MrBlahhhh/esp32-autosport/sim/buck.png

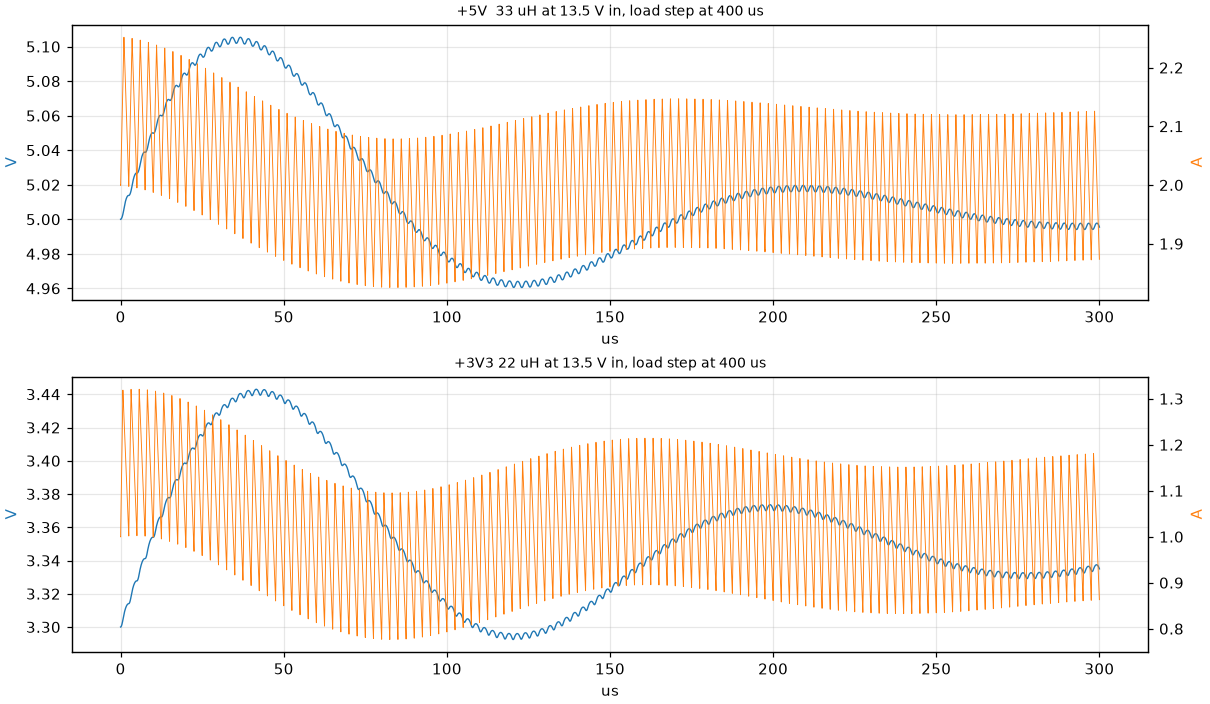
sim/buck.png
