MrBlahhhh/esp32-autosport/sim/firmware.png

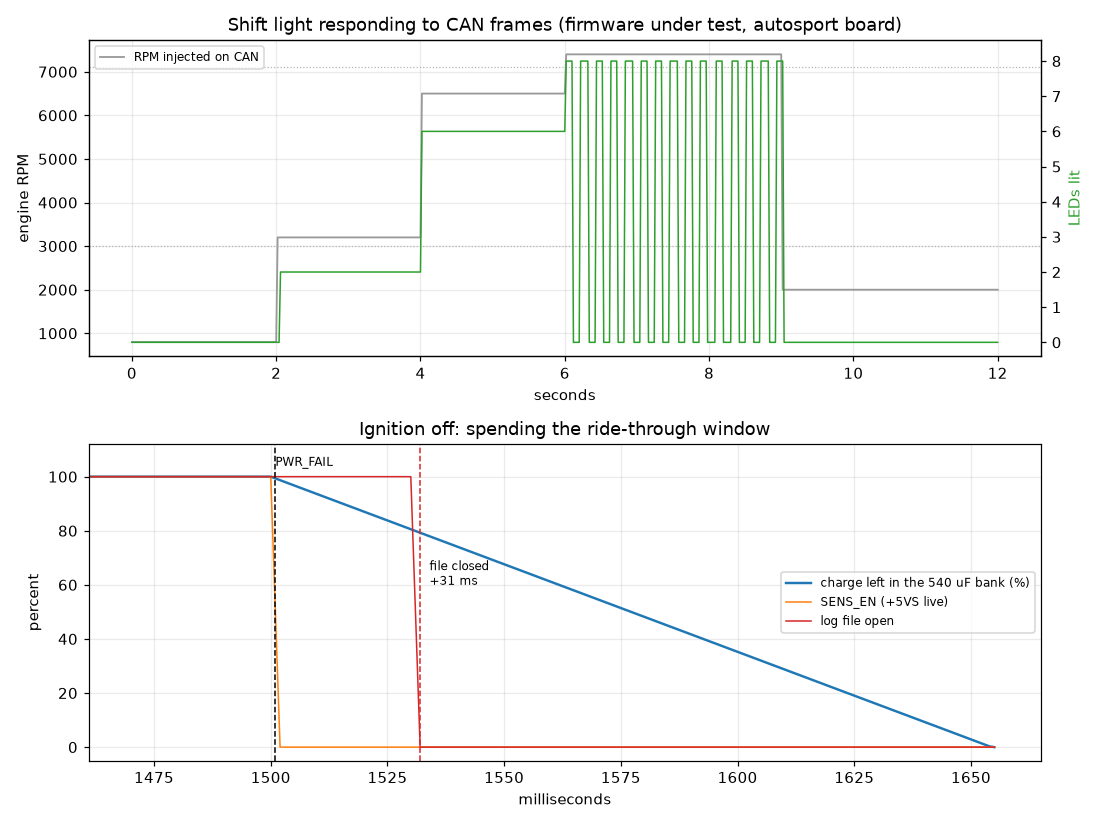
sim/firmware.png
