MrBlahhhh/esp32-autosport/sim/frontend.png

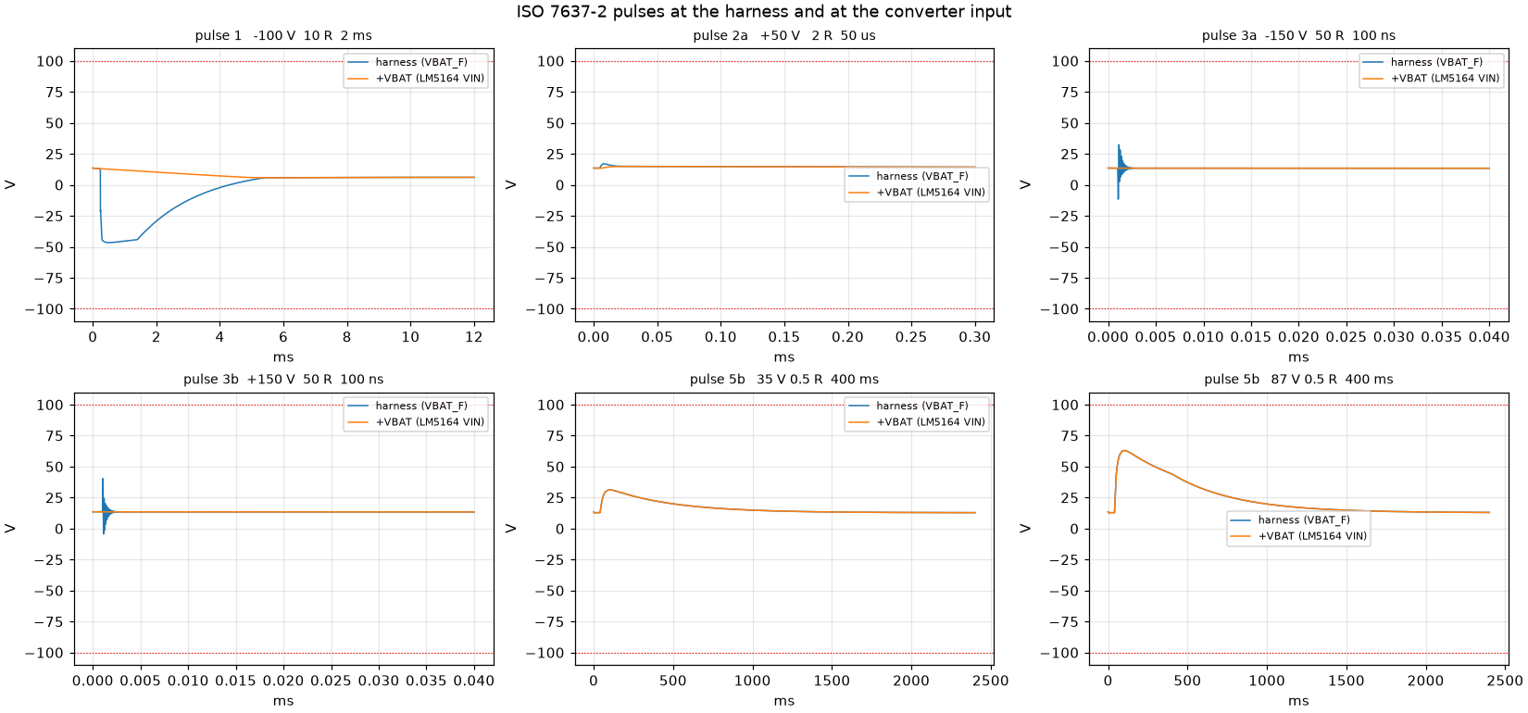
sim/frontend.png
