MrBlahhhh/esp32-autosport/gen/generate_schematic.py

#!/usr/bin/env python3
"""
Generate the KiCad schematic for the ESP32-S3 CAN + microSD automotive logger.

The netlist below is the single source of truth: every component lists its
pins and the net each pin lands on.  Symbol geometry and -- critically --
pin numbering come from the official KiCad symbol libraries, so pin numbers
are never hand-typed here.

Output: <project>/*.kicad_sch (hierarchical, one sheet per functional block),
        <project>/bom.csv, <project>/netlist.txt

Usage:  python3 gen/generate_schematic.py [--symbol-dir /usr/share/kicad/symbols]
"""

import argparse
import csv
import math
import os
import re
import uuid

# --------------------------------------------------------------------------
# S-expression reading (only what we need: pin geometry + raw symbol text)
# --------------------------------------------------------------------------

TOKEN = re.compile(r'"(?:[^"\\]|\\.)*"|\(|\)|[^\s()]+')


def parse_sexp(text):
    toks = TOKEN.findall(text)
    pos = 0

    def read():
        nonlocal pos
        tok = toks[pos]
        pos += 1
        if tok == "(":
            out = []
            while toks[pos] != ")":
                out.append(read())
            pos += 1
            return out
        return tok

    out = []
    while pos < len(toks):
        out.append(read())
    return out


def unquote(s):
    if s.startswith('"'):
        return s[1:-1].replace('\\"', '"').replace("\\\\", "\\")
    return s


def children(node, tag):
    return [c for c in node if isinstance(c, list) and c and c[0] == tag]


def _property_spans(text):
    """[(start, end)] of each top-level (property ...) block in a symbol."""
    spans = []
    depth, i, in_str = 0, 0, False
    start = None
    while i < len(text):
        ch = text[i]
        if in_str:
            if ch == "\\":
                i += 2
                continue
            if ch == '"':
                in_str = False
        elif ch == '"':
            in_str = True
        elif ch == "(":
            if depth == 1 and start is None and text.startswith("(property ", i):
                start = i
            depth += 1
        elif ch == ")":
            depth -= 1
            if depth == 1 and start is not None:
                spans.append((start, i + 1))
                start = None
        i += 1
    return spans


# The schematic format this generator emits, and the symbol-library format its
# embedded definitions were validated against.  KiCad opens older schematics and
# upgrades them on load, so emitting the 7.0 format is safe on 7, 8 and 9 alike.
SCH_FORMAT_VERSION = "20230121"          # KiCad 7.0
VALIDATED_SYMBOL_VERSION = "20241209"    # KiCad 9.0 symbol libraries


def find_symbol_dir():
    """Locate the stock KiCad symbol libraries on Windows, macOS or Linux."""
    import glob as _glob

    for var in ("KICAD9_SYMBOL_DIR", "KICAD8_SYMBOL_DIR", "KICAD7_SYMBOL_DIR",
                "KICAD6_SYMBOL_DIR"):
        path = os.environ.get(var)
        if path and os.path.isdir(path):
            return path

    patterns = [
        r"C:\Program Files\KiCad\*\share\kicad\symbols",
        r"C:\Program Files (x86)\KiCad\*\share\kicad\symbols",
        "/Applications/KiCad/KiCad.app/Contents/SharedSupport/symbols",
        "/usr/share/kicad/symbols",
        "/usr/local/share/kicad/symbols",
        os.path.expanduser("~/.local/share/kicad/*/symbols"),
    ]
    found = []
    for pat in patterns:
        found.extend(p for p in _glob.glob(pat) if os.path.isdir(p))
    if found:
        # Highest KiCad version wins when several are installed.
        return sorted(found)[-1]
    return None


class SymbolLibs:
    """Reads the installed KiCad symbol libraries."""

    def __init__(self, symbol_dir):
        self.symbol_dir = symbol_dir
        self._parsed = {}
        self._raw = {}
        self.lib_version = None

    def _load(self, lib):
        if lib in self._parsed:
            return
        path = os.path.join(self.symbol_dir, lib + ".kicad_sym")
        if not os.path.exists(path):
            raise SystemExit("symbol library not found: " + path)
        text = open(path, encoding="utf-8").read().replace("\r\n", "\n")
        root = parse_sexp(text)[0]
        ver = children(root, "version")
        if ver and self.lib_version is None:
            self.lib_version = unquote(ver[0][1])
        self._parsed[lib] = {unquote(s[1]): s for s in children(root, "symbol")}

        # Byte-exact source text for each top-level symbol, so the definitions
        # we embed in the schematic are identical to the library's.
        # One indent level is two spaces (7.0 libraries) or one tab (9.0).
        raw = {}
        for m in re.finditer(r'^(?:  |\t)\(symbol "([^"]+)"', text, re.M):
            start = m.start()
            depth, i, in_str = 0, start, False
            while i < len(text):
                ch = text[i]
                if in_str:
                    if ch == "\\":
                        i += 2
                        continue
                    if ch == '"':
                        in_str = False
                elif ch == '"':
                    in_str = True
                elif ch == "(":
                    depth += 1
                elif ch == ")":
                    depth -= 1
                    if depth == 0:
                        i += 1
                        break
                i += 1
            raw[m.group(1)] = text[start:i]
        self._raw[lib] = raw

    def symbol(self, lib_id):
        lib, name = lib_id.split(":", 1)
        self._load(lib)
        if name not in self._parsed[lib]:
            raise SystemExit("symbol not found: " + lib_id)
        return self._parsed[lib][name]

    def has(self, lib_id):
        lib, name = lib_id.split(":", 1)
        if not os.path.exists(os.path.join(self.symbol_dir, lib + ".kicad_sym")):
            return False
        self._load(lib)
        return name in self._parsed[lib]

    def extends(self, lib_id):
        ext = children(self.symbol(lib_id), "extends")
        return unquote(ext[0][1]) if ext else None

    def properties(self, lib_id):
        out = {}
        for prop in children(self.symbol(lib_id), "property"):
            out[unquote(prop[1])] = unquote(prop[2])
        return out

    def raw(self, lib_id):
        """Library source for the symbol, renamed to its full lib_id.

        A schematic's lib_symbols cache cannot express `extends`: KiCad stores
        derived symbols flattened.  KiCad's own flattening keeps the parent's
        geometry but the child's property fields verbatim (positions and text
        effects included), so the splice must swap whole property blocks or
        ERC flags the cached copy as differing from the library's.
        """
        lib, name = lib_id.split(":", 1)
        self._load(lib)
        parent = self.extends(lib_id)
        if parent is None:
            text = self._raw[lib][name]
            return text.replace('(symbol "%s"' % name,
                                '(symbol "%s:%s"' % (lib, name), 1)

        text = self._raw[lib][parent]
        child = self._raw[lib][name]
        pspans = _property_spans(text)
        child_props = [child[a:b] for a, b in _property_spans(child)]
        if pspans and child_props:
            first, last = pspans[0][0], pspans[-1][1]
            indent = text[:first].rsplit("\n", 1)[-1]
            text = text[:first] + ("\n" + indent).join(child_props) + text[last:]
        # Sub-symbol names must follow the derived symbol, e.g. FOO_1_1.
        text = text.replace('(symbol "%s_' % parent, '(symbol "%s_' % name)
        text = text.replace('(symbol "%s"' % parent,
                            '(symbol "%s:%s"' % (lib, name), 1)
        return text

    def pins(self, lib_id):
        """[(number, name, local_x, local_y, angle, hidden)] resolving `extends`.

        Hidden pins matter: the ESP32 module symbol carries its GND pin 40 and
        exposed pad 41 as hidden pins that KiCad ties to GND by name.  We record
        them so the netlist documents the connection, but never draw a stub to
        an invisible pin.
        """
        parent = self.extends(lib_id)
        if parent:
            lib = lib_id.split(":", 1)[0]
            return self.pins(lib + ":" + parent)
        out = []
        for unit in children(self.symbol(lib_id), "symbol"):
            for pin in children(unit, "pin"):
                at = children(pin, "at")[0]
                num = unquote(children(pin, "number")[0][1])
                nam = unquote(children(pin, "name")[0][1])
                out.append((num, nam, float(at[1]), float(at[2]),
                            int(float(at[3])), "hide" in pin))
        return out


# --------------------------------------------------------------------------
# Geometry helpers
# --------------------------------------------------------------------------

def rotate(theta, vx, vy):
    """Rotate a sheet-space vector by the symbol placement angle (CCW, Y down)."""
    theta %= 360
    if theta == 0:
        return (vx, vy)
    if theta == 90:
        return (vy, -vx)
    if theta == 180:
        return (-vx, -vy)
    if theta == 270:
        return (-vy, vx)
    raise ValueError("unsupported rotation %r" % theta)


def pin_geometry(local_x, local_y, angle, theta):
    """Return (offset_from_origin, outward_unit_vector) in sheet space."""
    # Symbol space has Y up; the sheet has Y down.
    off = rotate(theta, local_x, -local_y)
    # A pin's `angle` points from its connection end *into* the body, so the
    # free (wire) direction is the opposite.
    out_ang = math.radians(angle + 180)
    d = rotate(theta, round(math.cos(out_ang)), -round(math.sin(out_ang)))
    return off, d


# Rails get a power symbol rather than a net-name label. It is what every
# schematic does, it makes a rail readable at a glance, and it removes the
# single largest source of labels on the page -- GND alone accounted for
# hundreds. Where KiCad has no stock symbol for a rail (+VBAT, +5VS, SD_VDD)
# a generic one is instantiated and its Value overridden: for a power symbol
# KiCad takes the net name from the Value field, so the rail is named
# correctly and drawn correctly. gen/validate.py re-extracts the netlist
# through KiCad and compares it node-for-node, so if that were wrong the
# build would fail rather than quietly merge two rails.
RAILS = {
    "GND":    ("power:GND",   "GND"),
    "+3V3":   ("power:+3V3",  "+3V3"),
    "+5V":    ("power:+5V",   "+5V"),
    "VBUS":   ("power:VBUS",  "VBUS"),
    "+VBAT":  ("power:+BATT", "+VBAT"),
    "+5VS":   ("power:+BATT", "+5VS"),
    "SD_VDD": ("power:+BATT", "SD_VDD"),
}


def power_placement(libs, lib_id, ex, ey, d):
    """Where to put a power symbol so its pin lands at (ex, ey) facing -d."""
    angle = libs.pins(lib_id)[0][4]
    want = (-d[0], -d[1])
    for theta in (0, 90, 180, 270):
        off, ds = pin_geometry(0.0, 0.0, angle, theta)
        if ds == want:
            return snap(ex - off[0]), snap(ey - off[1]), theta
    return snap(ex), snap(ey), 0


# --------------------------------------------------------------- wiring ----
# A net drawn as two name labels is correct and unreadable. Where a net has
# exactly two pins in the whole design and both are on one sheet, the two
# parts can simply be placed next to each other and joined with a wire --
# which is what the connection actually is. Everything else (rails, shared
# nodes, anything crossing a sheet) keeps a symbol or a label, because those
# genuinely are one-to-many.

def pin_count(net):
    n = 0
    for sh in SHEETS:
        for p in sh["parts"]:
            n += sum(1 for v in p["pins"].values() if v == net)
    return n


def wire_pairs(sh):
    """[(partA, pinA, partB, pinB, net)] for this sheet's two-pin nets."""
    here = [p for p in sh["parts"] if not p["prefix"].startswith("#")]
    out, used = [], set()
    for net in sorted({v for p in here for v in p["pins"].values()}):
        if net in RAILS or pin_count(net) != 2:
            continue
        ends = [(p, num) for p in here for num, v in p["pins"].items() if v == net]
        if len(ends) != 2:
            continue                      # the other end is on another sheet
        (pa, na), (pb, nb) = ends
        if pa["ref"] in used or pb["ref"] in used:
            continue                      # one cluster per part keeps it simple
        used.add(pa["ref"])
        used.add(pb["ref"])
        out.append((pa, na, pb, nb, net))
    return out


def label_rotation(direction):
    return {(1, 0): 0, (-1, 0): 180, (0, -1): 90, (0, 1): 270}[direction]


def label_justify(direction):
    """Which way the text runs from the anchor.

    Every label used to be justified left, so one pointing back at its own
    component ran its text straight over the body -- RON_5V across R4,
    SW_5V across L1. Text has to run away from the part, not into it.
    """
    return "right" if direction in ((-1, 0), (0, 1)) else "left"


def mm(v):
    v = round(v, 4)
    return ("%f" % v).rstrip("0").rstrip(".") or "0"


NS = uuid.UUID("6f1d7d1e-6d3e-5a2b-9c44-2b6f0f0a1c77")


def det_uuid(key):
    return str(uuid.uuid5(NS, key))


# --------------------------------------------------------------------------
# Board description
# --------------------------------------------------------------------------

PROJECT = "esp32s3-can-sd-logger"
TITLE = "ESP32-S3 CAN + microSD Automotive Logger"
REV = "B"
DATE = "2026-08-11"   # the date of the last electrical change, not of the
                      # last regeneration -- update it when the netlist moves
COMPANY = "geekopolis"

R0805 = "Resistor_SMD:R_0805_2012Metric"
C0805 = "Capacitor_SMD:C_0805_2012Metric"
C1206 = "Capacitor_SMD:C_1206_3216Metric"
SOT23 = "Package_TO_SOT_SMD:SOT-23"
SOT236 = "Package_TO_SOT_SMD:SOT-23-6"
# NOTE: confirm the exposed-pad size against TI's DDA package drawing before layout.
# TI DDA0008B (SO PowerPAD-8): pad max 2.71x3.4mm, TI land 2.95x4.9mm copper
# with a 2.71x3.4mm solder-mask-defined opening -- this footprint matches it.
SO8EP = ("Package_SO:SOIC-8-1EP_3.9x4.9mm_P1.27mm_"
         "EP2.95x4.9mm_Mask2.71x3.4mm_ThermalVias")
SOIC8 = "Package_SO:SOIC-8_3.9x4.9mm_P1.27mm"
SMC = "Diode_SMD:D_SMC"
SMA = "Diode_SMD:D_SMA"
SOD123 = "Diode_SMD:D_SOD-123"
LED0805 = "LED_SMD:LED_0805_2012Metric"
JST4 = "Connector_JST:JST_PH_B4B-PH-K_1x04_P2.00mm_Vertical"
JST8 = "Connector_JST:JST_PH_B8B-PH-K_1x08_P2.00mm_Vertical"
HDR3 = "Connector_PinHeader_2.54mm:PinHeader_1x03_P2.54mm_Vertical"
HDR4 = "Connector_PinHeader_2.54mm:PinHeader_1x04_P2.54mm_Vertical"
HDR6 = "Connector_PinHeader_2.54mm:PinHeader_1x06_P2.54mm_Vertical"
HDR8 = "Connector_PinHeader_2.54mm:PinHeader_1x08_P2.54mm_Vertical"
SOT235 = "Package_TO_SOT_SMD:SOT-23-5"
SOT233 = "Package_TO_SOT_SMD:SOT-23"   # TLV431 is a 3-pin SOT-23
SJ2 = "Jumper:SolderJumper-2_P1.3mm_Open_Pad1.0x1.5mm"
SJ2B = "Jumper:SolderJumper-2_P1.3mm_Bridged_Pad1.0x1.5mm"
SJ3 = "Jumper:SolderJumper-3_P1.3mm_Open_Pad1.0x1.5mm"
SJ3B12 = "Jumper:SolderJumper-3_P1.3mm_Bridged12_Pad1.0x1.5mm"
TP = "TestPoint:TestPoint_Pad_D1.5mm"
MH = "MountingHole:MountingHole_3.2mm_M3"

# Each entry: (lib_id, value, footprint, {pin: net}, mpn, note)
SHEETS = []


def sheet(name, filename, description):
    s = {"name": name, "file": filename, "desc": description, "parts": []}
    SHEETS.append(s)
    return s


_TOL_RE = re.compile(r"\s+(\d+(?:\.\d+)?\s*%)$")
_VOLT_RE = re.compile(r"\s+(\d+(?:\.\d+)?\s*V)$")


def split_value(value):
    """'100nF 16V' -> ('100nF', '16V', ''), '1k 0.1%' -> ('1k', '', '0.1%').

    A rating packed into the VALUE field is invisible to anything that
    parses the schematic: a review tool reading "1k 0.1%" sees no usable
    resistance and reports the part as unvalued, which is what happened to
    34 capacitors and 16 resistors here. Only a trailing voltage or
    tolerance token is peeled off, so "600R" and
    "0.2A PTC" are left exactly as they are.
    """
    tol = volt = ""
    m = _TOL_RE.search(value)
    if m:
        tol = m.group(1).replace(" ", "")
        value = value[:m.start()]
    m = _VOLT_RE.search(value)
    if m:
        volt = m.group(1).replace(" ", "")
        value = value[:m.start()]
    return value.strip(), volt, tol


# Part numbers for the generic passives and the two ferrites.
#
# These used to be left blank on the theory that JLC's order flow auto-matches
# an 0805 resistor from value + package, which it does. That stopped being good
# enough the moment the boards were going to be hand-assembled: buying the
# parts loose needs a real number for every line, not just the interesting
# ones. Every entry below is the part JLCPCB's own matcher chose on a live
# order run (2026-08-13), so ordering from LCSC gets the same component the
# assembly house would have fitted.
#
# Keyed on the Comment string export_fab.py writes, which is value + voltage +
# tolerance -- so 100nF100V and 100nF16V stay distinct. That distinction is
# load-bearing: C2/C5/C16 sit on +VBAT and must be the 100 V part.
GENERIC_LCSC = {
    "0466002.NR": "C187595",
    "100": "C17408",
    "100k": "C149504",
    "100k1%": "C5713386",
    "100nF100V": "C28233",
    "100nF16V": "C49678",
    "10k": "C17414",
    "10k0.1%": "C856630",
    "10nF100V": "C128805",
    "10uF100V": "C6872041",
    "10uF16V": "C13585",
    "12.7k1%": "C2933300",
    "121k": "C17438",
    "15k0.1%": "C728642",
    "1M": "C17514",
    "1k": "C17513",
    "1k0.1%": "C864177",
    "1nF50V": "C46653",
    "1uF16V": "C28323",
    "1uF50V": "C28323",
    "2.21k0.1%": "C865368",
    "2.2nF50V": "C28260",
    "2.49k": "C2930178",
    "20.5k": "C2933365",
    "22uF16V": "C12891",
    "27.4k1%": "C2930188",
    "270pF50V": "C1732",
    "31.6k": "C49254250",
    "33": "C17634",
    "4.7k": "C17673",
    "4.7nF50V": "C1744",
    "44.2k": "C2960780",
    "47k": "C17713",
    "5.1k": "C27834",
    "57.6k": "C163405",
    "60.4": "C72998",
    "742792022": "C2661452",
    "742792625": "C1533835",
    "8.2k": "C17828",
    "95.3k": "C2930435",
}


def part(sh, prefix, lib_id, value, footprint, pins, mpn="", note="", nc=(),
         lcsc=""):
    base, volt, tol = split_value(value)
    sh["parts"].append(
        {
            "prefix": prefix,
            "lib_id": lib_id,
            "value": base,
            "voltage": volt,
            "tolerance": tol,
            "footprint": footprint,
            "pins": pins,
            "mpn": mpn,
            "note": note,
            "nc": set(nc),
            # Fall back to the generic table, keyed the same way export_fab.py
            # builds its Comment column (value + voltage + tolerance).
            # ...or by bare MPN. export_fab.py drops the manufacturer from
            # the Comment ("Wurth 742792022" -> "742792022"), so match the
            # last token too.
            "lcsc": lcsc or GENERIC_LCSC.get(base + volt + tol)
                    or GENERIC_LCSC.get(mpn)
                    or GENERIC_LCSC.get(mpn.split()[-1] if mpn else "", ""),
        }
    )


def R(sh, value, a, b, mpn="", note="", fp=R0805):
    part(sh, "R", "Device:R", value, fp, {"1": a, "2": b}, mpn, note)


def C(sh, value, a, b, fp=C0805, mpn="", note="", polarized=False):
    """`a` is pin 1. For a polarized part that is the + terminal, and the
    symbol must say so: a plain Device:C on an electrolytic land is right
    by luck rather than by construction, and neither ERC nor a reader can
    tell it from a reversed one."""
    lib = "Device:C_Polarized" if polarized else "Device:C"
    part(sh, "C", lib, value, fp, {"1": a, "2": b}, mpn, note)


def flag(sh, net):
    part(sh, "#FLG", "power:PWR_FLAG", "PWR_FLAG", "", {"1": net}, note="ERC power-source flag")


# ---------------------------------------------------------------- power ----
pw = sheet(
    "Power",
    "power.kicad_sch",
    "Reverse-battery protection, transient clamping, +5V / +3V3 / +5V sensor rails",
)

part(pw, "J", "Connector_Generic:Conn_01x04", "PWR + CAN harness", JST4,
     {"1": "VBAT_IN", "2": "GND", "3": "CAN_H", "4": "CAN_L"},
     "JST B4B-PH-K-S(LF)(SN)", "Pin 1 +12V, 2 GND, 3 CAN_H, 4 CAN_L "
     "(Autosport Labs harness order)", lcsc="C131334")
part(pw, "F", "Device:Fuse", "2A slow", "Fuse:Fuse_1206_3216Metric",
     {"1": "VBAT_IN", "2": "VBAT_F"}, "Littelfuse 0466002.NR",
     "Sacrificial: only opens on a hard fault, not on reverse polarity")
part(pw, "FB", "Device:L", "600R", "Inductor_SMD:L_1206_3216Metric",
     {"1": "VBAT_F", "2": "VBAT_FB"}, "Wurth 742792625", "Conducted-emissions bead")

# Ideal-diode reverse-battery block
part(pw, "U", "Power_Management:LM74700", "LM74700-Q1", SOT236,
     {"1": "VCAP", "2": "GND", "3": "VBAT_UVLO", "4": "+VBAT", "5": "GATE_RB", "6": "VBAT_FB"},
     "LM74700QDBVRQ1", "Ideal-diode controller; blocks reverse battery via Q1",
     lcsc="C2941042")
part(pw, "Q", "Device:Q_NMOS_GSD", "IPD068N10", "Package_TO_SOT_SMD:TO-252-3_TabPin2",
     {"1": "GATE_RB", "2": "VBAT_FB", "3": "+VBAT"}, "Infineon IPD068N10N3G",
     "Source to battery, drain to load: body diode blocks reverse polarity. "
     "The previously specified PSMN4R3-100BSE does not exist", lcsc="C88066")
C(pw, "1uF 50V", "VCAP", "VBAT_FB", mpn="", note="LM74700 charge-pump reservoir")
C(pw, "100nF 100V", "VBAT_FB", "GND",
  note="LM74700 ANODE input capacitor: the datasheet requires a minimum "
       "22nF at ANODE and this node is behind FB1 with nothing else on it")
R(pw, "100k", "VBAT_FB", "VBAT_UVLO", note="UVLO upper leg")
R(pw, "44.2k", "VBAT_UVLO", "GND",
  note="UVLO lower leg. Ratio 0.3065 against V_EN_IH 1.06/2.0/2.6V gives "
       "release at 3.5/6.5/8.5V. The earlier 25.5k assumed a 1.2V threshold "
       "and would not have started until 9.8V typical, 12.8V worst case")

# Ahead of Q1, not behind it. Clamping downstream of the reverse-battery FET
# leaves Q1 and the LM74700 exposed to whatever arrives on the harness: on a
# negative transient Q1 turns off and stands the whole pulse across its
# drain-source, and ISO 7637-2 pulse 1 (-100V) and 3a (-150V) both exceed its
# 100V rating. In front of the FET the clamp catches those first.
#
# Bidirectional, because a unidirectional part here would forward-conduct on
# a sustained reverse connection and blow the fuse -- which is exactly the
# outcome the ideal diode exists to avoid. SMCJ40CA stands off 40V either
# way, so -14V reverse battery is still Q1's job to block, and only real
# transients are clamped.
part(pw, "D", "Device:D_TVS", "SMCJ40CA", SMC, {"1": "VBAT_F", "2": "GND"},
     "Littelfuse SMCJ40CA",
     "40V standoff / 64.5V clamp @ 1500W, bidirectional: absorbs ISO 7637-2 "
     "pulse 5b load dump and the negative pulses, ahead of the FET. 40V not "
     "33V so the part stands off the declared 36V input top", lcsc="C80273")
C(pw, "100uF 100V", "+VBAT", "GND", fp="Capacitor_SMD:CP_Elec_10x10.5",
  mpn="Nichicon UCD2A101MNL1GS", polarized=True,
  note="Bulk hold-up; any 100uF >=80V SMD electrolytic on a 10x10.5 land "
       "works -- match in the JLC catalog at order. Pin 1 is +")
C(pw, "10uF 100V", "+VBAT", "GND", fp=C1206, note="Switcher input bypass")
C(pw, "100nF 100V", "+VBAT", "GND", note="HF bypass")

# Ride-through bank. The card in this thing is written continuously and the
# ignition is switched, so every drive ends in an unannounced power cut. With
# only the 100uF above, +VBAT falls through the converters' UVLO about 12 ms
# after the harness opens -- less than one SD block write on a slow card, so
# the file is left however the card happened to leave it.
#
# Energy is 0.5*C*(V^2 - Vmin^2), so it belongs here on +VBAT rather than on
# a 3.3V rail: the same capacitance is worth fifteen times as much at 12 V as
# it is at 3.3 V. From 12 V (the low end of a healthy battery) down to the
# 7 V the converters stop regulating at, 760 uF holds 36.1 mJ.
#
# 760 uF (100 + 2 x 330), not 540: the 16x22 can has the same land pattern as
# the 16x17.5 it replaces, so the extra 220 uF is free in copper. It is not
# free in inrush -- charging the bank through Q1's body diode gives the fuse
# an I2t burden proportional to C, so the 2 A nano fuse's margin drops from
# about 5x to about 3.6x. Still comfortable, but it is the number to watch if
# the bank ever grows again (gen/simulate.py, inrush study).
#
# 100 V rated, not 63 V: D1 clamps at 64.5 V and the declared input window
# already goes to 36 V.
for _ in range(2):
    C(pw, "330uF 100V", "+VBAT", "GND",
      fp="Capacitor_SMD:CP_Elec_16x22", polarized=True,
      note="Power-fail ride-through. With the sensor rail shed and the LEDs "
           "off the board draws about 0.35 W here, so the bank holds the "
           "rails up long enough to finish the block in flight and close the "
           "file. 16x22 rather than 16x17.5: the two footprints are identical "
           "in every copper and courtyard layer -- only the can is 4.5 mm "
           "taller -- so the extra 220 uF costs nothing but enclosure height. "
           "Any 330uF >=80V on a 16 mm land works; match in the JLC catalogue "
           "at order. Pin 1 is +")

# ---- power-fail detect ---------------------------------------------------
# Sensed on VBAT_F, ahead of Q1, which is the whole point: when the ignition
# opens, the harness side collapses at once while +VBAT coasts on the bank
# above. Q1 is already the isolating diode between them, so this costs no
# extra parts and gives the earliest possible warning. Sensing +VBAT instead
# would only notice once the ride-through had already started being spent.
#
# A bare divider into a GPIO will not do. The ESP32's input is only
# guaranteed high above 0.75*VDD and low below 0.25*VDD, so the real trip
# point could land anywhere from 11 V down to 3.7 V of harness -- and at
# 3.7 V the bank is long empty. The shunt reference makes it +/-1%.
R(pw, "100k 1%", "VBAT_F", "PFD_SENSE", note="Power-fail divider, upper leg")
R(pw, "12.7k 1%", "PFD_SENSE", "GND",
  note="Lower leg: trips at 1.24V * 112.7/12.7 = 11.00V on the harness, "
       "below anything a healthy battery does and far above the converters' "
       "dropout, so there is a whole ride-through between detect and death")
part(pw, "U", "Reference_Voltage:TL431DBZ", "TLV431A", SOT233,
     {"1": "PWR_FAIL", "2": "PFD_SENSE", "3": "GND"},
     "TLV431ASN1T1G",
     "Power-fail comparator. Below the trip point it stops conducting and "
     "R_pu takes PWR_FAIL high, so the interrupt is a rising edge and an "
     "absent or dead part reads as 'failing' rather than as 'fine'. "
     "PINOUT: this uses KiCad's TL431DBZ numbering (1 K, 2 REF, 3 A) on a "
     "plain SOT-23. Shunt references are NOT consistent between vendors in "
     "this package -- CONFIRM against the datasheet for the exact part "
     "ordered. If REF and A are swapped the part simply never conducts and "
     "PWR_FAIL sits permanently asserted: loud, harmless, and obvious on the "
     "bench, but it will not be caught by ERC or DRC", lcsc="C127592")
R(pw, "10k", "+3V3", "PWR_FAIL",
  note="Cathode pull-up. 10k gives the part 330uA, over the TLV431's 100uA "
       "minimum cathode current. A 2.5V TL431 would need 1mA and so a 2.2k "
       "here, and the divider below would have to change with it")
R(pw, "1M", "PWR_FAIL", "PFD_SENSE",
  note="Hysteresis, about 0.3V at the harness. Without it a battery sagging "
       "across the threshold on crank would chatter the interrupt")
C(pw, "1nF 50V", "PFD_SENSE", "GND",
  note="Just enough to keep switching noise off the reference. Larger would "
       "delay the very detection this exists to make early")

# ---- switched sensor excitation -----------------------------------------
# The ride-through only works if the load goes away with the power. LEDs and
# the SD card are firmware's to shed, but sensors on +5VS are external and
# draw whatever they draw -- four at 20 mA is 400 mW, which more than doubles
# the drain and would halve the numbers above. This switch is what makes the
# shed possible.
#
# Off by default: the gate is pulled to +5V through R_g, so the rail comes up
# only when firmware asserts SENS_EN, and it drops the instant the MCU stops
# driving. That is the correct failure direction for a rail that feeds a loom.
part(pw, "Q", "Device:Q_PMOS_GSD", "AO3401A", SOT23,
     {"1": "SENS_G", "2": "+5V", "3": "VSENS_SW"}, "Alpha & Omega AO3401A",
     "Sensor-rail load switch. Source to +5V, so the body diode points into "
     "the rail and the switch blocks with the gate high", lcsc="C15127")
R(pw, "100k", "+5V", "SENS_G", note="Holds the switch off when nothing drives it")
part(pw, "Q", "Device:Q_NMOS_GSD", "2N7002", SOT23,
     {"1": "SENS_EN_G", "2": "GND", "3": "SENS_G"}, "onsemi 2N7002",
     "Level shifter: the P-FET's gate has to be pulled to GND from 5V, and "
     "a 3.3V GPIO cannot do that directly", lcsc="C8545")
R(pw, "10k", "SENS_EN", "SENS_EN_G", note="GPIO series/gate resistor")
R(pw, "100k", "SENS_EN_G", "GND",
  note="Holds the level shifter off while the MCU is in reset")

# +5V rail
part(pw, "U", "Regulator_Switching:LM5164DDA", "LM5164 (5V)", SO8EP,
     {"1": "GND", "2": "+VBAT", "3": "EN_5V", "4": "RON_5V", "5": "FB_5V",
      "6": "PG_5V", "7": "BST_5V", "8": "SW_5V", "9": "GND"},
     "LM5164DDAR", "100V synchronous buck, ultra-low Iq. Non-automotive "
     "variant; the Q1 is scarce", lcsc="C477928")
R(pw, "100k", "+VBAT", "EN_5V", note="Enable tied to VIN (LM74700 already gates on UVLO)")
C(pw, "10nF 100V", "EN_5V", "GND", note="EN sits on a bare 100k to VBAT; this "
  "keeps a high-impedance enable node quiet in a vehicle")
R(pw, "31.6k", "RON_5V", "GND",
  note="RON = 5.0V x 2500 / 400kHz (Eq 12) -> 396kHz; tON = 237ns at the "
       "53.3V clamp, comfortably above the 50ns minimum")
C(pw, "2.2nF 50V", "BST_5V", "SW_5V",
  note="Bootstrap: datasheet mandates exactly 2.2nF X7R -- a larger value "
       "overstresses the internal VCC regulator and damages the device")
part(pw, "L", "Device:L", "33uH", "Inductor_SMD:L_Sunlord_SWPA8040S",
     {"1": "SW_5V", "2": "+5V"}, "Sunlord ASWPA8050S330MT",
     "Shielded molded, Isat 3A vs the 1.75A max peak limit", lcsc="C340244")
R(pw, "100k", "+5V", "FB_5V", note="FB upper: 1.2V ref -> 5.00V")
R(pw, "31.6k", "FB_5V", "GND", note="FB lower")
# Type-3 ripple injection (datasheet Table 6-1): the all-ceramic output has no
# ESR ripple for the COT comparator, so a SW-node RC ramp is AC-coupled into
# FB. Sized for ~20mV at FB with VIN = 14V nominal, per TI's design example.
R(pw, "121k", "SW_5V", "RAMP_5V", note="Ripple-injection ramp resistor RA")
C(pw, "2.2nF 50V", "RAMP_5V", "+5V", note="Ramp capacitor CA. 2.2nF, not 3.3nF: at 8 V in the injected ramp was 10.6 mV against the ~15 mV COT floor; the smaller CA buys x1.5")
C(pw, "270pF 50V", "RAMP_5V", "FB_5V", note="Ramp coupling capacitor CB")
C(pw, "22uF 16V", "+5V", "GND", fp=C1206)
C(pw, "22uF 16V", "+5V", "GND", fp=C1206)
C(pw, "100nF 16V", "+5V", "GND")
R(pw, "100k", "PG_5V", "+3V3", note="Power-good pull-up")

# +3V3 rail
part(pw, "U", "Regulator_Switching:LM5164DDA", "LM5164 (3V3)", SO8EP,
     {"1": "GND", "2": "+VBAT", "3": "EN_3V3", "4": "RON_3V3", "5": "FB_3V3",
      "6": "PG_3V3", "7": "BST_3V3", "8": "SW_3V3", "9": "GND"},
     "LM5164DDAR", "Second buck straight off the battery: a shorted 5V "
     "sensor harness cannot brown out the MCU", lcsc="C477928")
# This converter's own input capacitors. It had none: it shared the 5 V
# island's pair, 12.6 mm away across the board, which puts that whole
# distance in the switching loop. The LM5164 chops the full battery
# voltage in nanoseconds, and the loop inductance turns into VIN ringing
# and radiated noise. Two more parts is a cheap fix for it.
C(pw, "100nF 100V", "+VBAT", "GND",
  note="3V3 buck HF input bypass -- must sit at U3's VIN pin")
C(pw, "10uF 100V", "+VBAT", "GND", fp=C1206,
  note="3V3 buck bulk input, at the VIN pin")
R(pw, "100k", "+VBAT", "EN_3V3")
C(pw, "10nF 100V", "EN_3V3", "GND", note="EN noise immunity, as for the 5V rail")
R(pw, "20.5k", "RON_3V3", "GND",
  note="RON = 3.3V x 2500 / 400kHz (Eq 12) -> 402kHz; tON = 154ns at the "
       "53.3V clamp, above the 50ns minimum")
C(pw, "2.2nF 50V", "BST_3V3", "SW_3V3",
  note="Bootstrap: datasheet-mandated 2.2nF X7R, do not increase")
part(pw, "L", "Device:L", "22uH", "Inductor_SMD:L_Sunlord_SWPA8040S",
     {"1": "SW_3V3", "2": "+3V3"}, "Sunlord ASWPA8050S220MT",
     "Same automotive series as L1. C340243 verified against the live JLC "
     "catalogue 2026-08-12: 22uH, 3A Isat, 8x8mm -- one part number below "
     "L1's C340244, which is the 33uH of the same series",
     lcsc="C340243")
R(pw, "100k", "+3V3", "FB_3V3", note="FB upper: 1.2V ref -> 3.28V")
R(pw, "57.6k", "FB_3V3", "GND", note="FB lower")
R(pw, "95.3k", "SW_3V3", "RAMP_3V3", note="Ripple-injection ramp resistor RA")
C(pw, "2.2nF 50V", "RAMP_3V3", "+3V3", note="Ramp capacitor CA, sized as on the 5 V rail for ramp amplitude at low battery")
C(pw, "270pF 50V", "RAMP_3V3", "FB_3V3", note="Ramp coupling capacitor CB")
C(pw, "22uF 16V", "+3V3", "GND", fp=C1206)
C(pw, "22uF 16V", "+3V3", "GND", fp=C1206)
C(pw, "100nF 16V", "+3V3", "GND")
R(pw, "100k", "PG_3V3", "+3V3")
part(pw, "D", "Device:D_Zener", "3.6V 300mW", "Diode_SMD:D_SOD-323",
     {"1": "+3V3", "2": "GND"}, "onsemi MM3Z3V6T1G",
     "Rail clamp: an analog input shorted to battery back-feeds ~1.6mA "
     "through its BAT54S into +3V3; with the MCU asleep the rail would "
     "otherwise float above the ESP32's 3.6V absolute maximum", lcsc="C116949")

# 5V sensor excitation, fused separately from the board 5V
part(pw, "PF", "Device:Polyfuse", "0.2A PTC", "Resistor_SMD:R_1206_3216Metric",
     {"1": "VSENS_SW", "2": "VSENS_F"}, "Bourns MF-MSMF020",
     "Resettable: a shorted sensor wire trips this, not the board. Now behind "
     "the load switch, so a short is also something firmware can clear by "
     "dropping SENS_EN, rather than waiting for the fuse to cool",
     lcsc="C719178")
part(pw, "FB", "Device:L", "600R", "Inductor_SMD:L_0805_2012Metric",
     {"1": "VSENS_F", "2": "+5VS"}, "Wurth 742792022")
C(pw, "10uF 16V", "+5VS", "GND", fp=C1206)
part(pw, "TP", "Connector:TestPoint", "PG_5V", TP, {"1": "PG_5V"})
part(pw, "TP", "Connector:TestPoint", "PG_3V3", TP, {"1": "PG_3V3"})
part(pw, "D", "Device:D_Zener", "SMAJ6.0A", SMA, {"1": "+5VS", "2": "GND"},
     "Littelfuse SMAJ6.0A",
     "Clamps harness-injected transients on the sensor 5V. 6.0V standoff, "
     "not 5.0V: a 5.0V part on a 5.0V rail leaks up to 800uA continuously", lcsc="C223993")

part(pw, "D", "Device:LED", "green", LED0805, {"1": "PWR_LED_K", "2": "+3V3"},
     lcsc="C2297",  # KT-0805G, 525 nm emerald green, verified 2026-08-13
     note="The board's only LED: +3V3 is up, so the whole supply chain came "
          "through -- battery, ideal diode, and both converters")
R(pw, "1k", "PWR_LED_K", "GND")

for net in ["+VBAT", "+5V", "+3V3", "+5VS", "GND"]:
    part(pw, "TP", "Connector:TestPoint", net, TP, {"1": net})
for net in ["GND", "+VBAT", "VBAT_FB", "+5V", "+3V3", "+5VS", "VBUS", "SD_VDD"]:
    flag(pw, net)
for _ in range(4):
    part(pw, "H", "Mechanical:MountingHole", "M3", MH, {})

# ------------------------------------------------------------------ MCU ----
mc = sheet("MCU", "mcu.kicad_sch", "ESP32-S3-WROOM-1 module, USB-C, boot/reset, break-out")

part(mc, "U", "RF_Module:ESP32-S3-WROOM-1", "ESP32-S3-WROOM-1-N16R8",
     "RF_Module:ESP32-S3-WROOM-1",
     {
         "1": "GND", "2": "+3V3", "3": "MCU_EN",
         "4": "AIN3", "5": "AIN4", "6": "VBAT_SNS", "7": "SD_PWR_EN",
         "8": "PWR_FAIL", "9": "SENS_EN", "10": "CAN_TX", "11": "CAN_RX",
         "12": "SD_CD", "13": "USB_DM", "14": "USB_DP",
         "15": "IO3", "16": "IO46",
         "17": "SD_D3", "18": "SD_D2", "19": "SD_D1", "20": "SD_D0",
         "21": "SD_CMD", "22": "SD_CLK", "23": "CAN_S",
         "24": "SPI_CS", "25": "LED_DIN_MCU", "26": "IO45", "27": "MCU_BOOT",
         "31": "I2C_SDA", "32": "I2C_SCL",
         "33": "SPI_SCK", "34": "SPI_MISO", "35": "SPI_MOSI",
         "36": "UART_RX", "37": "UART_TX", "38": "AIN2", "39": "AIN1",
         # Hidden in the symbol; KiCad bonds them to GND by name.
         "40": "GND", "41": "GND",
     },
     "ESP32-S3-WROOM-1-N16R8", lcsc="C2913202",
     note="16MB flash / 8MB octal PSRAM. Pins 28-30 (IO35/36/37) are consumed by "
     "the octal PSRAM and must stay unconnected. IO3/IO45/IO46 on the spare "
     "header are strapping pins -- leave floating at boot.",
     nc=("28", "29", "30"))

R(mc, "10k", "+3V3", "MCU_EN")
C(mc, "1uF 16V", "MCU_EN", "GND", note="EN reset delay")
part(mc, "SW", "Switch:SW_Push", "RESET", "Button_Switch_SMD:SW_SPST_TL3342",
     {"1": "MCU_EN", "2": "GND"}, "TL3342F160QG",
     "Genuine E-Switch is scarce at LCSC; any 5.2mm gull-wing tact fits",
     lcsc="C2886898")
R(mc, "10k", "+3V3", "MCU_BOOT")
part(mc, "SW", "Switch:SW_Push", "BOOT", "Button_Switch_SMD:SW_SPST_TL3342",
     {"1": "MCU_BOOT", "2": "GND"}, "TL3342F160QG", lcsc="C2886898")
C(mc, "10uF 16V", "+3V3", "GND", fp=C1206)
C(mc, "100nF 16V", "+3V3", "GND")
C(mc, "100nF 16V", "+3V3", "GND")

part(mc, "J", "Connector:USB_C_Receptacle_USB2.0_16P", "USB-C",
     "Connector_USB:USB_C_Receptacle_HRO_TYPE-C-31-M-12",
     {"A1": "GND", "B1": "GND", "A12": "GND", "B12": "GND", "S1": "GND",
      "A4": "VBUS_IN", "B4": "VBUS_IN", "A9": "VBUS_IN", "B9": "VBUS_IN",
      "A5": "USB_CC1", "B5": "USB_CC2",
      "A6": "USB_DP_CON", "B6": "USB_DP_CON",
      "A7": "USB_DM_CON", "B7": "USB_DM_CON"},
     mpn="HRO TYPE-C-31-M-12", lcsc="C165948",
     note="Programming / CDC console only -- not a power path in the car",
     nc=("A8", "B8"))
R(mc, "5.1k", "USB_CC1", "GND")
R(mc, "5.1k", "USB_CC2", "GND")
part(mc, "PF", "Device:Polyfuse", "0.5A hold", "Resistor_SMD:R_1206_3216Metric",
     {"1": "VBUS_IN", "2": "VBUS_R"}, "Bourns MF-MSMF050", lcsc="C17313")

# ---- USB overvoltage cutoff -----------------------------------------------
# Simulation showed a 'USB' brick that puts 9 V on VBUS lifting the whole
# +5V rail to 8.4 V through D5, over the TJA1051's 6 V absolute maximum --
# the buck can source but not sink, so the rail goes wherever the brick
# pushes it. A plain 5.1k CC pull-down means a compliant PD source never
# offers more than 5 V; this guards against the QC bricks and dumb "12 V
# USB" adapters that do not ask.
#
# Same recipe as the sensor-rail switch, with the TLV431 as the brain: the
# P-FET passes VBUS_R to VBUS by default (gate held low), and above the
# 1.24 V x 127.4/27.4 = 5.77 V trip the TLV431 conducts, the PNP pulls the
# gate up to the source, and the switch opens. 5.77 V sits above any
# compliant 5 V source's 5.25 V ceiling and below the 6 V it protects.
# With the switch open the P-FET body diode points back at the brick, so
# nothing leaks through. Off-the-shelf OVP switches were checked first:
# the TPS25200 class cuts off around 7 V, which is no protection at all
# for a 6 V limit.
part(mc, "Q", "Device:Q_PMOS_GSD", "AO3401A", SOT23,
     {"1": "VBUS_G", "2": "VBUS_R", "3": "VBUS"}, "Alpha & Omega AO3401A",
     "USB OVP series switch: source faces the connector so the body diode "
     "blocks toward the board when the switch is open", lcsc="C15127")
R(mc, "100k", "VBUS_G", "GND", note="Switch on by default")
part(mc, "Q", "Device:Q_PNP_BEC", "MMBT3906", SOT23,
     {"1": "VBUS_OV", "2": "VBUS_R", "3": "VBUS_G"}, "ST(Semtech) MMBT3906",
     "Pulls the P-FET gate to its source on overvoltage. NOTE: this was "
     "C8544 until 2026-08-12, which is an S9018 -- an NPN, and not this part "
     "at all. Ordering it would have assembled the wrong polarity into the "
     "USB over-voltage cutoff and left the protection inoperative. Verified "
     "against the live catalogue: C84105 is an ST(Semtech) MMBT3906, PNP, "
     "SOT-23, 40 V", lcsc="C84105")
R(mc, "10k", "VBUS_R", "VBUS_OV",
  note="Holds the PNP off while the TLV431 is not conducting")
part(mc, "U", "Reference_Voltage:TL431DBZ", "TLV431A", SOT233,
     {"1": "VBUS_OV", "2": "VBUS_OVS", "3": "GND"}, "TLV431ASN1T1G",
     "OVP comparator; conducts above the divider trip and opens the switch. "
     "Same pinout caution as the power-fail TLV431: confirm K/REF/A against "
     "the datasheet of the exact part ordered", lcsc="C127592")
R(mc, "100k 1%", "VBUS_R", "VBUS_OVS", note="OVP divider upper leg")
R(mc, "27.4k 1%", "VBUS_OVS", "GND",
  note="Trip at 1.24V x 127.4/27.4 = 5.77V: above a compliant source's "
       "5.25V ceiling, below the TJA1051's 6V absolute maximum")

part(mc, "D", "Device:D_Schottky", "40V 1A", SOD123, {"1": "+5V", "2": "VBUS"},
     "PMEG4010", "OR-ing: bench USB can power the board, but the 5V buck "
     "(5.00V) reverse-biases it whenever the car is connected", lcsc="C193342")
C(mc, "10uF 16V", "VBUS", "GND", fp=C1206)
C(mc, "100nF 16V", "VBUS", "GND",
  note="USBLC6-2SC6 VBUS pin decoupling; the ST datasheet asks for this "
       "alongside the bulk part for surge-layout reasons")
part(mc, "U", "Power_Protection:USBLC6-2SC6", "USBLC6-2SC6", SOT236,
     {"1": "USB_DP_CON", "2": "GND", "3": "USB_DM_CON",
      "4": "USB_DM", "5": "VBUS", "6": "USB_DP"},
     "USBLC6-2SC6", "USB ESD clamp, behind the OVP switch so its own 5.5 V "
     "VBUS-pin limit is honoured too", lcsc="C7519")
# The CC pins are the FIRST contacts a plug mates, so they take the cable's
# static charge before anything else -- and until now they landed on bare
# 5.1k resistors. Same part as the data-line clamp, one more instance; a
# fried CC pin is invisible damage that presents as "USB stopped working".
part(mc, "U", "Power_Protection:USBLC6-2SC6", "USBLC6-2SC6", SOT236,
     {"1": "USB_CC1", "2": "GND", "3": "USB_CC2", "5": "VBUS"},
     "USBLC6-2SC6", "CC-pin ESD clamp; flow-through pins 4/6 unused",
     lcsc="C7519", nc=("4", "6"))

part(mc, "J", "Connector_Generic:Conn_01x04", "UART0", HDR4,
     {"1": "+3V3", "2": "UART_TX", "3": "UART_RX", "4": "GND"})
part(mc, "J", "Connector_Generic:Conn_01x04", "I2C / Qwiic", HDR4,
     {"1": "GND", "2": "+3V3", "3": "I2C_SDA", "4": "I2C_SCL"})
R(mc, "4.7k", "+3V3", "I2C_SDA")
R(mc, "4.7k", "+3V3", "I2C_SCL")


# SPI breakout for MCP2515 / CC1101 / MAX6675 / etc.
part(mc, "J", "Connector_Generic:Conn_01x06", "SPI", HDR6,
     {"1": "+3V3", "2": "GND", "3": "SPI_SCK", "4": "SPI_MISO",
      "5": "SPI_MOSI", "6": "SPI_CS"},
     note="IO40 SCK / IO41 MISO / IO42 MOSI / IO47 CS -- GPIO-matrix SPI")

# WS2812 shift-light header: true 5 V data via AHCT buffer (3.3 V TTL-friendly
# input, 5 V rail). IO48 is RMT-capable and not a strapping pin.
R(mc, "10k", "SPI_CS", "+3V3",
  note="Holds an attached slave deselected until firmware drives IO47; the "
       "module pin's reset-state pull is the unknown")
R(mc, "33", "LED_DIN_MCU", "LED_DIN_A",
  note="Edge-rate limit into the level shifter")
part(mc, "U", "74xGxx:74AHCT1G125", "74AHCT1G125", SOT235,
     {"1": "GND", "2": "LED_DIN_A", "3": "GND", "4": "LED_DIN", "5": "+5V"},
     # NOT C7975 -- that is an LMV324IPWRG4 quad op-amp in TSSOP-14, and out
     # of stock besides. JLC resolved our part number to it and warned that
     # the footprint did not match SOT-23-5, which is how the error surfaced.
     # C7484 verified against the live JLC catalogue 2026-08-12: TI
     # SN74AHCT1G125DBVR, SOT-23-5, extended.
     "SN74AHCT1G125DBVR", lcsc="C7484",
     note="5 V buffer so WS2812 DIN is a real 5 V rail, not 3.3 V hoping")
C(mc, "100nF 16V", "+5V", "GND", note="AHCT decoupling")
R(mc, "100", "LED_DIN", "LED_DIN_J",
  note="Series termination into the strip. The buffer drove the connector "
       "directly, and a WS2812 strip is metres of unterminated lead")
part(mc, "PF", "Device:Polyfuse", "0.5A hold", "Resistor_SMD:R_1206_3216Metric",
     {"1": "+5V", "2": "LED_5V"}, "Bourns MF-MSMF050",
     "Fused tap for the shift-light strip (8x WS2812 ~0.5 A worst case)",
     lcsc="C17313")
part(mc, "J", "Connector_Generic:Conn_01x03", "WS2812", HDR3,
     {"1": "LED_5V", "2": "LED_DIN_J", "3": "GND"},
     note="Shift-light header: +5V / 5V-logic DIN / GND")

# Remaining free GPIOs after SPI + WS2812. All three are strapping pins.
# IO45 selects VDD_SPI voltage and IO46 the boot mode; both must read low at
# reset. The internal pull-downs do that on a bare board, but this is a user
# header -- anything attached that pulls IO45 high sets the flash supply to
# 1.8V and the module simply will not boot.
R(mc, "10k", "IO3", "GND", note="Strapping pin held low at boot")
R(mc, "10k", "IO45", "GND", note="Strapping pin: VDD_SPI = 3.3V")
R(mc, "10k", "IO46", "GND", note="Strapping pin: normal boot mode")
part(mc, "J", "Connector_Generic:Conn_01x06", "Spare IO", HDR6,
     {"1": "IO3", "2": "IO45", "3": "IO46",
      "4": "PWR_FAIL", "5": "SENS_EN", "6": "GND"},
     note="IO3/IO45/IO46 are strapping pins, each with a 10k pull-down -- "
          "anything attached must not fight them at boot. Pins 4 and 5 are "
          "no longer spare: IO15 is the power-fail interrupt and IO16 is the "
          "sensor-rail enable. They stay on the header as probe points, so "
          "the ride-through can be watched on a scope without unsoldering "
          "anything, but nothing else may drive them. The ground pin is here "
          "so a probe or a ribbon has a return")
part(mc, "J", "Connector_Generic:Conn_01x04", "Rail break-out", HDR4,
     {"1": "+5V", "2": "+3V3", "3": "GND", "4": "GND"})

# ------------------------------------------------------------- SD card ----
sd = sheet("SD Card", "sdcard.kicad_sch",
           "microSD in 4-bit SDMMC mode with a switchable card supply")

part(sd, "J", "Connector:Micro_SD_Card_Det1", "microSD push-pull",
     "Connector_Card:microSD_HC_Hirose_DM3D-SF",
     {"1": "SD_D2_C", "2": "SD_D3_C", "3": "SD_CMD_C", "4": "SD_VDD",
      "5": "SD_CLK_C", "6": "GND", "7": "SD_D0_C", "8": "SD_D1_C",
      "9": "SD_CD", "10": "GND"},
     "Hirose DM3D-SF", "Push-pull socket; DET is the card-present switch",
     lcsc="C719027")

# The card contacts are touched at every swap -- by hand, in a paddock, in
# whatever the weather is doing -- and until now the only thing between an
# insertion-day static discharge and the ESP32's GPIO was the ESP32's own
# ~2 kV pin diodes. Two quad arrays clamp every card contact. VP goes to
# +3V3 rather than the switched SD_VDD so the clamps reference a rail that
# is alive even while the card power is cycled off.
part(sd, "U", "Power_Protection:SRV05-4", "SRV05-4",
     "Package_TO_SOT_SMD:SOT-23-6",
     {"1": "SD_CLK_C", "3": "SD_CMD_C", "4": "SD_D0_C", "6": "SD_D1_C",
      "2": "GND", "5": "+3V3"},
     "Semtech SRV05-4.TCT", "Card-slot ESD clamp, CLK/CMD/D0/D1",
     lcsc="C13612")
part(sd, "U", "Power_Protection:SRV05-4", "SRV05-4",
     "Package_TO_SOT_SMD:SOT-23-6",
     {"1": "SD_D2_C", "3": "SD_D3_C", "4": "SD_CD",
      "2": "GND", "5": "+3V3"},
     "Semtech SRV05-4.TCT", "Card-slot ESD clamp, D2/D3/CD",
     lcsc="C13612", nc=("6",))

# The SD bus is the most likely thing to need a scope at bring-up, and both
# of these nets otherwise exist only as fine-pitch SMD pads.
part(sd, "TP", "Connector:TestPoint", "SD_CLK", TP, {"1": "SD_CLK_C"})
part(sd, "TP", "Connector:TestPoint", "SD_CMD", TP, {"1": "SD_CMD_C"})

part(sd, "Q", "Device:Q_PMOS_GSD", "DMG2301L", SOT23,
     {"1": "SD_PG", "2": "+3V3", "3": "SD_VDD"}, "DMG2301L",
     "High-side switch so firmware can power-cycle a wedged card",
     lcsc="C7472914")
R(sd, "100k", "+3V3", "SD_PG", note="Default off")
part(sd, "Q", "Device:Q_NMOS_GSD", "2N7002", SOT23,
     {"1": "SD_EN_G", "2": "GND", "3": "SD_PG"}, "2N7002",
     "Level shift for the P-ch gate. Prefer an AEC-Q101 equivalent: the "
     "standard 2N7002 is not automotive qualified", lcsc="C8545")
R(sd, "1k", "SD_PWR_EN", "SD_EN_G",
  note="Series gate resistor. 10k here divided against R27 100k and left "
       "only 0.24V over the 2N7002 cold-end threshold")
R(sd, "100k", "SD_EN_G", "GND")
C(sd, "10uF 16V", "SD_VDD", "GND", fp=C1206)
C(sd, "100nF 16V", "SD_VDD", "GND")

for sig in ["CLK", "CMD", "D0", "D1", "D2", "D3"]:
    R(sd, "33", "SD_" + sig, "SD_%s_C" % sig, note="Series damping")
for sig in ["CMD", "D0", "D1", "D2", "D3"]:
    R(sd, "10k", "SD_VDD", "SD_%s_C" % sig,
      note="Espressif's recommended value; pulled to the switched rail so "
           "nothing back-feeds a powered-down card")
# Card detect is a slow mechanical contact, not a bus line, so it keeps the
# weaker pull-up -- less standing current with a card inserted.
R(sd, "47k", "+3V3", "SD_CD", note="Card-detect pull-up")

# ----------------------------------------------------------------- CAN ----
cn = sheet("CAN", "can.kicad_sch", "Isolated-ground CAN 2.0B node with selectable termination")

part(cn, "U", "Interface_CAN_LIN:TJA1051T-3", "TJA1051T/3", SOIC8,
     {"1": "CAN_TX", "2": "GND", "3": "+5V", "4": "CAN_RX", "5": "+3V3",
      "6": "CANL_T", "7": "CANH_T", "8": "CAN_S"},
     "TJA1051T/3,118", lcsc="C58988",
     note="5V bus drive with a 3.3V VIO pin, so no level shifting to the ESP32")
C(cn, "100nF 16V", "+5V", "GND")
C(cn, "100nF 16V", "+3V3", "GND")
R(cn, "10k", "CAN_S", "GND", note="Default to normal (non-silent) mode")

part(cn, "L", "Device:L_Coupled", "51uH", "esp32autosport:L_CommonMode_TDK_ACT45B",
     {"1": "CANH_T", "2": "CAN_H", "3": "CANL_T", "4": "CAN_L"},
     "TDK ACT45B-510-2P-TL003",
     "AEC-Q200 CAN choke; footprint pads renumbered so symbol winding 1-2 is "
     "the package's top (1-4) winding", lcsc="C76584")
part(cn, "JP", "Jumper:SolderJumper_2_Open", "TERM (default OFF)", SJ2,
     {"1": "CAN_H", "2": "TERM_A"},
     note="Ships OPEN: unterminated. Bridge the pads only when this board is "
          "an END node on its own bus. A vehicle's bus -- OBD-II diagnostics "
          "included -- is already terminated at both ends, and a third 120 "
          "ohm across the pair takes it to about 40 ohm and can stop it "
          "working. Defaulting terminated made that an easy mistake to make")
R(cn, "60.4", "TERM_A", "CAN_SPLIT", note="Split termination upper half")
R(cn, "60.4", "CAN_SPLIT", "CAN_L", note="Split termination lower half")
C(cn, "4.7nF 50V", "CAN_SPLIT", "GND", note="Split-termination common-mode stabiliser")
part(cn, "D", "Device:D_TVS", "SMAJ26CA", SMA, {"1": "CAN_H", "2": "GND"},
     "Diodes Inc SMAJ26CA-13-F", "Bidirectional bus clamp", lcsc="C134976")
part(cn, "D", "Device:D_TVS", "SMAJ26CA", SMA, {"1": "CAN_L", "2": "GND"},
     "Diodes Inc SMAJ26CA-13-F", lcsc="C134976")
part(cn, "TP", "Connector:TestPoint", "CAN_H", TP, {"1": "CAN_H"})
part(cn, "TP", "Connector:TestPoint", "CAN_L", TP, {"1": "CAN_L"})

# -------------------------------------------------------------- analog ----
an = sheet("Analog Inputs", "analog.kicad_sch",
           "4 sensor channels with jumper-selected dividers and pull-up bias")

part(an, "J", "Connector_Generic:Conn_01x08", "Sensor harness", JST8,
     {"1": "+5VS", "2": "AIN1_IN", "3": "AIN2_IN", "4": "AIN3_IN",
      "5": "AIN4_IN", "6": "GND", "7": "GND", "8": "+5VS"},
     "JST B8B-PH-K-S(LF)(SN)", "Two 5V and two ground pins so sensors can "
     "be paired up", lcsc="C157974")

for n in range(1, 5):
    inp, node, out = "AIN%d_IN" % n, "AIN%d_A" % n, "AIN%d" % n
    # Transient clamp at the connector, ahead of everything else. The BAT54S
    # pairs downstream are 200mA signal Schottkys with no pulse energy rating,
    # so on an unshielded harness they were the only thing standing between an
    # ISO 7637 pulse and the ADC. Bidirectional because pulse 1 is negative.
    # 40V standoff clears a sustained short to the 36V top of the input window,
    # which a lower standoff part would sit in conduction on until it failed.
    part(an, "D", "Device:D_TVS", "SMAJ40CA", SMA, {"1": inp, "2": "GND"},
         "Littelfuse SMAJ40CA",
         "Ch%d harness transient clamp (bidirectional, 400W)" % n, lcsc="C223989")
    R(an, "1k 0.1%", inp, node,
      note="Ch%d series/fault-current limit; 0.1%% thin film -- it is inside "
           "the divider chain, so its tolerance is a gain error" % n)
    part(an, "JP", "Jumper:SolderJumper_2_Open", "PULLUP%d" % n, SJ2,
         {"1": "+5VS", "2": "AIN%d_PU" % n},
         note="Close for 2-wire NTC / open-collector sensors")
    R(an, "2.49k", "AIN%d_PU" % n, node, note="Ch%d bias resistor" % n)
    R(an, "10k 0.1%", node, out,
      note="Ch%d divider upper leg, 0.1%% thin film for AFR-grade accuracy" % n)
    part(an, "JP", "Jumper:SolderJumper_2_Open", "BYPASS%d" % n, SJ2,
         {"1": node, "2": out},
         note="Close for a raw 0-3.3V sensor (shorts the upper leg)")
    part(an, "JP", "Jumper:SolderJumper_3_Bridged12", "RANGE%d (default 0-5V)" % n, SJ3B12,
         {"2": out, "1": "AIN%d_R1" % n, "3": "AIN%d_R2" % n},
         note="Ships BRIDGED 1-2 = the 0-5V range, which is what almost every "
              "automotive sensor is. Cut 1-2 and bridge 2-3 for 0-16V; cut "
              "1-2 and leave both open for no divider (then close BYPASS%d "
              "for a raw 0-3.3V sensor). Defaulting to 0-5V also means the "
              "firmware's DIVIDER_GAIN matches the board as shipped" % n)
    R(an, "15k 0.1%", "AIN%d_R1" % n, "GND",
      note="0-5V range: 5.0V in -> ~2.88V at the ADC (1k series included); "
           "exact scale is a firmware calibration constant")
    R(an, "2.21k 0.1%", "AIN%d_R2" % n, "GND",
      note="0-16V range: 16.0V in -> ~2.67V at the ADC (1k series included)")
    C(an, "100nF 16V", out, "GND", note="Ch%d anti-alias / ADC charge reservoir" % n)
    # One SOT-23 series pair: GND -> signal -> +3V3, so the node is clamped a
    # Schottky drop either side of the rails.
    part(an, "D", "Device:D_Schottky_Dual_Series_AKC", "BAT54S", SOT23,
         {"1": "GND", "3": out, "2": "+3V3"}, "MDD BAT54S",
         "Ch%d rail clamp (both polarities)" % n, lcsc="C408389")

# Precision path for the four channels: the ESP32-S3 ADC is only good for
# ±1-2% even calibrated, which is ±0.2 AFR on a 0-5V wideband output. The
# ADS1115 (16-bit delta-sigma, on the existing I2C bus at 0x48) shares the
# conditioned AINx nodes, so firmware chooses per channel: fast-and-rough on
# the internal ADC, or slow-and-accurate here. Inputs are clamped to +3V3 by
# the BAT54S pairs, within the ADS1115's VDD+0.3V absolute maximum.
part(an, "U", "Analog_ADC:ADS1115IDGS", "ADS1115",
     "Package_SO:VSSOP-10_3x3mm_P0.5mm",
     {"1": "GND", "3": "GND", "4": "AIN1", "5": "AIN2", "6": "AIN3",
      "7": "AIN4", "8": "+3V3", "9": "I2C_SDA", "10": "I2C_SCL"},
     "ADS1115IDGSR", lcsc="C37593",
     note="16-bit 4-ch I2C ADC for AFR-grade accuracy; ADDR to GND = 0x48",
     nc=("2",))
C(an, "100nF 16V", "+3V3", "GND", note="ADS1115 decoupling")

R(an, "100k", "+VBAT", "VBAT_SNS", note="Battery monitor: divide by 11")
R(an, "8.2k", "VBAT_SNS", "GND",
  note="Divide by 13.2, not 11: at 36V the 11:1 divider put 3.27V on the "
       "pin, above the ADC's usable 3.1V, so the reading saturated near "
       "the top of the declared input window")
C(an, "100nF 16V", "VBAT_SNS", "GND")
part(an, "D", "Device:D_Schottky_Dual_Series_AKC", "BAT54S", SOT23,
     {"1": "GND", "3": "VBAT_SNS", "2": "+3V3"}, "MDD BAT54S", "Battery-monitor clamp", lcsc="C408389")


# --------------------------------------------------------------------------
# Reference designators
# --------------------------------------------------------------------------

def assign_refs():
    counters = {}
    for sh in SHEETS:
        for p in sh["parts"]:
            pre = p["prefix"]
            counters[pre] = counters.get(pre, 0) + 1
            p["ref"] = "%s%d" % (pre, counters[pre])


# --------------------------------------------------------------------------
# Placement
# --------------------------------------------------------------------------

PAGE_W, PAGE_H = 594.0, 297.0   # A2 width, A3 height: sheets grow sideways
MARGIN_X, MARGIN_TOP, MARGIN_BOT = 12.0, 18.0, 22.0
STUB = 5.08
LABEL_ALLOWANCE = 15.0   # rails are power symbols and pairs are wired now
# Breathing room. The packer used to fill each column to the bottom of the
# page before starting the next, which reads as a dense stripe down the left
# with the rest of an A3 sheet empty. ROW_PAD and COL_GAP set the minimum,
# and any height a column does not need is then shared out between its parts.
ROW_PAD, ROW_MIN, COL_GAP, ROW_SLACK_MAX = 10.16, 17.78, 12.7, 15.24
# Sheets are packed against A3 and then given the smallest standard page the
# drawing actually fits on. A CAN transceiver and its bus is a 130 x 70 mm
# drawing; left on A3 it is a stamp in the corner of an empty page, and
# "fit to window" then renders it too small to read.
PAPERS = [("A5", 210.0, 148.0), ("A4", 297.0, 210.0), ("A3", 420.0, 297.0),
          ("A2", 594.0, 420.0)]
# A2 is here because the Power sheet outgrew A3 when the ride-through bank,
# the power-fail detector and the sensor-rail switch went on it. The
# alternative was splitting Power in two, which would put the front end and
# the rails it feeds on different pages -- worse to read than a wide page.
GRID = 1.27


def snap(v):
    return round(v / GRID) * GRID


def symbol_extent(libs, lib_id, theta):
    xs, ys = [0.0], [0.0]
    for _, _, lx, ly, ang, hidden in libs.pins(lib_id):
        if hidden:
            continue
        off, d = pin_geometry(lx, ly, ang, theta)
        xs += [off[0], off[0] + d[0] * STUB]
        ys += [off[1], off[1] + d[1] * STUB]
    return min(xs), max(xs), min(ys), max(ys)


WIRE_GAP = 8.89          # host pin to satellite pin, with room for the
                         # net name to sit on the wire between them


def match_part(sh, value, nets, taken):
    """Find a part on this sheet by value and the exact nets it touches.

    Same identification the PCB placement tables use, and for the same
    reason: it survives reference renumbering, which happens on every run.
    """
    for p in sh["parts"]:
        if p["ref"] in taken or p["value"] != value:
            continue
        if nets is not None and set(p["pins"].values()) != set(nets):
            continue
        taken.add(p["ref"])
        return p
    return None


def pin_clearance(libs, part):
    """How far the text has to stand off, so it clears any vertical stub."""
    up = down = 0.0
    for _n, _nm, lx, ly, ang, hid in libs.pins(part["lib_id"]):
        if hid:
            continue
        _o, dv = pin_geometry(lx, ly, ang, part["theta"])
        if dv == (0, -1):
            up = STUB + 3.81
        elif dv == (0, 1):
            down = STUB + 3.81
    part["_bup"], part["_bdown"] = up, down


def apply_blocks(libs, sh):
    """Place the hand-drawn blocks that live on this sheet.

    Returns the parts the blocks own, so the column packer leaves them
    alone -- a block travels as one drawing, not as loose symbols.
    """
    import sch_blocks
    owned, taken, placed = {}, set(), []
    for blk in sch_blocks.BLOCKS:
        if blk["sheet"] != sh["name"]:
            continue
        anchor = match_part(sh, blk["anchor"][0], blk["anchor"][1], taken)
        if anchor is None:
            continue
        anchor["_block"] = True
        anchor["_own_ext"] = anchor["ext"]
        pin_clearance(libs, anchor)
        members = []
        for value, nets, dx, dy, rot in blk["parts"]:
            part = match_part(sh, value, nets, taken)
            if part is None:
                raise SystemExit(
                    "block %r wants a %r on %s and this sheet has none left"
                    % (blk["anchor"][0], value, sorted(nets or [])))
            part["theta"] = rot
            part["ext"] = symbol_extent(libs, part["lib_id"], rot)
            part["_up"] = part["_down"] = 0.0
            part["_block"] = True
            pin_clearance(libs, part)
            members.append((part, dx, dy))
        placed.append({"blk": blk, "anchor": anchor, "members": members})
        for part, dx, dy in members:
            owned[part["ref"]] = (anchor, dx, dy)
    sh["_blocks"] = placed
    return owned


def orient_two_pin(libs, p, num, want):
    """Rotation that makes pin `num` of a two-pin part face `want`."""
    for theta in (0, 90, 180, 270):
        for n, _nm, lx, ly, ang, hid in libs.pins(p["lib_id"]):
            if hid or n != num:
                continue
            _off, d = pin_geometry(lx, ly, ang, theta)
            if d == want:
                return theta
    return p.get("theta", 0)


def attach_satellites(libs, sh, owned=()):
    """Park each two-pin partner right on the pin it serves.

    The satellite sits WIRE_GAP beyond the host pin, facing back at it, so
    the connection is a single straight wire rather than a pair of labels.

    Parts a hand-drawn block already owns are off limits. This runs after
    apply_blocks and writes position and rotation last, so without the
    guard it quietly re-parked block members -- the 5 V bootstrap cap ended
    up rotated and 6 mm from where the block drew its wire, and the only
    symptom was two nets KiCad could no longer name.
    """
    sats = {}
    for pa, na, pb, nb, net in wire_pairs(sh):
        if pa["ref"] in owned or pb["ref"] in owned:
            continue
        host, hnum, sat, snum = pa, na, pb, nb
        if len(pa["pins"]) < len(pb["pins"]):
            host, hnum, sat, snum = pb, nb, pa, na
        if len(sat["pins"]) != 2:
            continue                       # only two-pin parts travel
        hoff = hd = None
        for n, _nm, lx, ly, ang, hid in libs.pins(host["lib_id"]):
            if not hid and n == hnum:
                hoff, hd = pin_geometry(lx, ly, ang, host["theta"])
        if hd is None:
            continue
        theta = orient_two_pin(libs, sat, snum, (-hd[0], -hd[1]))
        soff = None
        for n, _nm, lx, ly, ang, hid in libs.pins(sat["lib_id"]):
            if not hid and n == snum:
                soff, _ = pin_geometry(lx, ly, ang, theta)
        if soff is None:
            continue
        sat["theta"] = theta
        sat["ext"] = symbol_extent(libs, sat["lib_id"], theta)
        sats[sat["ref"]] = {
            "host": host["ref"], "theta": theta,
            "dx": hoff[0] + hd[0] * WIRE_GAP - soff[0],
            "dy": hoff[1] + hd[1] * WIRE_GAP - soff[1],
            "wire": (hoff, hd, soff),
            "host_pin": hnum, "sat_pin": snum, "net": net,
        }
    sh["_sats"] = sats
    return sats


def place(libs):
    """Lay parts out in columns, sized to the widest symbol in each column."""
    for sh in SHEETS:
        for p in sh["parts"]:
            # Two-pin parts read best lying horizontally, but KiCad draws some
            # of them vertically and others horizontally, so ask the symbol
            # which way its pins point rather than hard-coding a list.
            visible = [pin for pin in libs.pins(p["lib_id"]) if not pin[5]]
            p["theta"] = 0
            if len(visible) == 2:
                dirs = {pin_geometry(x, y, a, 0)[1] for _, _, x, y, a, _ in visible}
                if dirs <= {(0, 1), (0, -1)}:
                    p["theta"] = 90
            p["ext"] = symbol_extent(libs, p["lib_id"], p["theta"])
            up = down = 0.0
            for _n, _nm, lx, ly, ang, hid in libs.pins(p["lib_id"]):
                if hid:
                    continue
                _o, dv = pin_geometry(lx, ly, ang, p["theta"])
                if dv == (0, -1):
                    up = STUB + 3.81
                elif dv == (0, 1):
                    down = STUB + 3.81
            p["_up"], p["_down"] = up, down

        blocks = apply_blocks(libs, sh)
        # Grow the anchor so the packer reserves room for the whole drawing.
        for ref, (anchor, dx, dy) in blocks.items():
            part = next(q for q in sh["parts"] if q["ref"] == ref)
            px0, px1, py0, py1 = part["ext"]
            ax0, ax1, ay0, ay1 = anchor["ext"]
            anchor["ext"] = (min(ax0, px0 + dx), max(ax1, px1 + dx),
                             min(ay0, py0 + dy), max(ay1, py1 + dy))
        # ...and for the wires, which reach past the parts they connect.
        for entry in sh.get("_blocks", []):
            anchor, blk = entry["anchor"], entry["blk"]
            pts = [q for poly in blk["wires"] for q in poly]
            if not pts:
                continue
            ax0, ax1, ay0, ay1 = anchor["ext"]
            anchor["ext"] = (min([ax0] + [q[0] for q in pts]),
                             max([ax1] + [q[0] for q in pts]),
                             min([ay0] + [q[1] for q in pts]),
                             max([ay1] + [q[1] for q in pts]))

        # Satellites ride with their host, so they are not packed separately.
        sats = attach_satellites(libs, sh, blocks)
        for ref, info in sats.items():
            host = next(q for q in sh["parts"] if q["ref"] == info["host"])
            sx0, sx1, sy0, sy1 = next(q for q in sh["parts"]
                                      if q["ref"] == ref)["ext"]
            hx0, hx1, hy0, hy1 = host["ext"]
            host["ext"] = (min(hx0, sx0 + info["dx"]), max(hx1, sx1 + info["dx"]),
                           min(hy0, sy0 + info["dy"]), max(hy1, sy1 + info["dy"]))

        columns, col, y = [], [], MARGIN_TOP
        usable = PAGE_H - MARGIN_TOP - MARGIN_BOT
        for p in sh["parts"]:
            if p["ref"] in sats or p["ref"] in blocks:
                continue
            x0, x1, y0, y1 = p["ext"]
            # Leave room for the reference and value text above and below the
            # body, otherwise adjacent rows of passives print on top of each
            # other.
            h = max((y1 - y0) + ROW_PAD + p["_up"] + p["_down"], ROW_MIN)
            if col and y + h > MARGIN_TOP + usable:
                columns.append(col)
                col, y = [], MARGIN_TOP
            p["_h"], p["_y"] = h, y
            col.append(p)
            y += h
        if col:
            columns.append(col)
        # Share out whatever height the column did not need.
        for col in columns:
            spare = usable - sum(p["_h"] for p in col)
            slack = min(spare / max(len(col), 1), ROW_SLACK_MAX)
            if slack <= 0:
                continue
            for i, p in enumerate(col):
                p["_y"] += slack * i
        x = MARGIN_X
        for col in columns:
            left = min(p["ext"][0] for p in col)
            right = max(p["ext"][1] for p in col)
            cx = x - left + LABEL_ALLOWANCE
            for p in col:
                p["x"] = snap(cx)
                p["y"] = snap(p["_y"] - p["ext"][2])
            x = cx + right + LABEL_ALLOWANCE + COL_GAP
        for ref, (anchor, dx, dy) in blocks.items():
            part = next(q for q in sh["parts"] if q["ref"] == ref)
            part["x"], part["y"] = snap(anchor["x"] + dx), snap(anchor["y"] + dy)
        # Satellites take their position from the host they hang off.
        for ref, info in sats.items():
            host = next(q for q in sh["parts"] if q["ref"] == info["host"])
            sat = next(q for q in sh["parts"] if q["ref"] == ref)
            sat["x"] = snap(host["x"] + info["dx"])
            sat["y"] = snap(host["y"] + info["dy"])
        sh["width_used"] = x
        # The title block eats the bottom right corner, so leave it clear.
        need_h = max([p["y"] + p["ext"][3] for p in sh["parts"]] or [0]) + 30.0
        sh["paper"] = next((nm for nm, pw, ph in PAPERS
                            if x <= pw and need_h <= ph), PAPERS[-1][0])
        # The packer wraps on height but never on width, so a sheet that grew
        # wide simply ran off the page: two symbols on the power sheet landed
        # at x = 422.9 on a 420 mm page, where ERC reported them unconnected
        # and nothing else complained. Fail loudly instead.
        if x > PAGE_W:
            raise SystemExit(
                "sheet %r needs %.0f mm of width but the page is %.0f mm -- "
                "%d columns. Widen the page or split the sheet."
                % (sh["name"], x, PAGE_W, len(columns)))


# --------------------------------------------------------------------------
# Serialisation
# --------------------------------------------------------------------------

FONT = "(effects (font (size 1.27 1.27)) %s)"


def emit_symbol(libs, sh, p, sheet_uuid):
    lines = []
    su = det_uuid("sym:%s:%s" % (sh["file"], p["ref"]))
    x0, x1, y0, y1 = p["ext"]
    lines.append(
        '  (symbol (lib_id "%s") (at %s %s %d) (unit 1)\n'
        "    (in_bom %s) (on_board yes) (dnp no)\n"
        '    (uuid %s)'
        % (p["lib_id"], mm(p["x"]), mm(p["y"]), p["theta"],
           "no" if p["prefix"].startswith("#") else "yes", su)
    )
    # Reference sits above the body and value below -- but a pin leaving the
    # top or bottom takes a stub and then a label or power symbol with it, and
    # the text landed straight on top of that: "LM5164 (5V)" printed through
    # the GND symbol under U2. Clear the whole stub where a pin goes that way.
    up, down = p.get("_up", 0.0), p.get("_down", 0.0)
    ref_y = p["y"] + y0 - 2.0 - up
    val_y = p["y"] + y1 + 2.0 + down
    ref_x = val_x = p["x"]
    # Inside a hand-drawn block the parts sit a few millimetres apart, and
    # the packer's generous text offsets then print one part's value through
    # the next part's body. Tuck the fields alongside instead, the way they
    # sit in a schematic drawn by hand: beside a vertical part, above and
    # below one lying on its side.
    if p.get("_block"):
        # An anchor's extent has been grown to reserve room for the whole
        # block, so field placement has to use the part's own body -- else
        # the anchor's reference floats off at the top of the drawing.
        x0, x1, y0, y1 = p.get("_own_ext", p["ext"])
        # Beside only for a part decidedly taller than it is wide. An IC that
        # is square-ish has pins out of both sides, and its fields then print
        # over the very labels those pins carry -- "USBLC6-2SC6" straight
        # through USB_DM. Above and below is where the room is.
        if y1 - y0 <= 1.6 * (x1 - x0):
            # A pin leaving the top or bottom takes a stub and then a label
            # or a power symbol with it, and the text lands on that: the
            # buffer printed "74AHCT1G125" straight through the ground
            # symbol under it. Clear the whole stub, as the packer does.
            ref_y = p["y"] + y0 - 1.27 - p.get("_bup", 0.0)
            val_y = p["y"] + y1 + 2.03 + p.get("_bdown", 0.0)
        else:
            ref_x = val_x = p["x"] + x1 + 1.27
            ref_y, val_y = p["y"] - 1.27, p["y"] + 1.78
    # A power symbol's name belongs on the far side of its body from the pin
    # it hangs off, or it lands on whatever that pin belongs to: "+3V3"
    # printed over "R16" on the very resistor it was feeding.
    if p.get("_pwr_dir"):
        dx, dy = p["_pwr_dir"]
        if dy < 0:
            val_y = p["y"] + y0 - 2.0
        elif dy > 0:
            val_y = p["y"] + y1 + 2.0
        else:
            val_y = p["y"] + 1.27
            val_x = p["x"] + (x1 + 2.0 if dx > 0 else x0 - 2.0)
    # A power symbol's reference (#PWR003) is noise -- the rail name in the
    # Value field is the label. KiCad hides these by convention and so do we,
    # along with the flags'.
    anon = p["prefix"].startswith("#")
    props = [("Reference", p["ref"], ref_x, ref_y, anon),
             ("Value", p["value"], val_x, val_y, p["lib_id"] == "power:PWR_FLAG"),
             ("Footprint", p["footprint"], val_x, val_y, True),
             ("Datasheet", "~", val_x, val_y, True)]
    if p.get("voltage"):
        props.append(("Voltage", p["voltage"], val_x, val_y, True))
    if p.get("tolerance"):
        props.append(("Tolerance", p["tolerance"], val_x, val_y, True))
    if p["mpn"]:
        props.append(("MPN", p["mpn"], val_x, val_y, True))
    if p["note"]:
        props.append(("Note", p["note"], val_x, val_y, True))
    # A property's angle is applied *on top of* the symbol's rotation, so a
    # rotated part needs its text counter-rotated to stay horizontal.
    # ...except at 180, where counter-rotating would print the text upside
    # down. KiCad only ever writes field angles of 0 or 90; a part flipped
    # end for end keeps its text the right way up.
    text_angle = 0 if p["theta"] == 180 else (360 - p["theta"]) % 360
    just = " (justify left)" if ref_x != p["x"] else ""
    for name, value, px, py, hide in props:
        # No control characters in a property string, ever. A literal
        # newline inside one is accepted by KiCad's loader but silently
        # breaks its connectivity pass: every symbol after it in the file
        # drops out of the netlist and ERC reports hundreds of dangling
        # wires with no hint of the cause. One "\n" in a part note cost an
        # evening of bisecting to find.
        clean = " ".join(value.replace('"', "'").split())
        lines.append(
            '    (property "%s" "%s" (at %s %s %d)\n      %s\n    )'
            % (name, clean, mm(px), mm(py), text_angle,
               "(effects (font (size 1.27 1.27))%s %s)"
               % (just, "hide" if hide else ""))
        )
    for num, _, _, _, _, _ in libs.pins(p["lib_id"]):
        lines.append('    (pin "%s" (uuid %s))'
                     % (num, det_uuid("pin:%s:%s:%s" % (sh["file"], p["ref"], num))))
    lines.append(
        '    (instances\n      (project "%s"\n        (path "/%s/%s" (reference "%s") (unit 1))\n      )\n    )'
        % (PROJECT, ROOT_UUID, sheet_uuid, p["ref"])
    )
    lines.append("  )")
    return "\n".join(lines)


def on_segment(px, py, a, b, eps=0.01):
    """Is (px, py) on the axis-aligned segment a--b?

    Block wires are drawn on the 1.27 mm grid and so are the pins they
    land on, so exact arithmetic would nearly do; eps covers the halves
    and thirds that creep in from symbol geometry.
    """
    (x1, y1), (x2, y2) = a, b
    if abs(y1 - y2) < eps:
        return (abs(py - y1) < eps
                and min(x1, x2) - eps <= px <= max(x1, x2) + eps)
    if abs(x1 - x2) < eps:
        return (abs(px - x1) < eps
                and min(y1, y2) - eps <= py <= max(y1, y2) + eps)
    dx, dy = x2 - x1, y2 - y1
    t = ((px - x1) * dx + (py - y1) * dy) / (dx * dx + dy * dy)
    return (0 <= t <= 1
            and abs(x1 + t * dx - px) < eps and abs(y1 + t * dy - py) < eps)


def wire_seg(x1, y1, x2, y2, uid):
    return ("  (wire (pts (xy %s %s) (xy %s %s))\n"
            "    (stroke (width 0) (type default))\n"
            "    (uuid %s)\n  )" % (mm(x1), mm(y1), mm(x2), mm(y2), uid))


def junction(x, y, uid):
    return ("  (junction (at %s %s) (diameter 0) (color 0 0 0 0)\n"
            "    (uuid %s)\n  )" % (mm(x), mm(y), uid))


HIER_LABEL = (
    '  (hierarchical_label "%s" (shape %s) (at %s %s %d)\n'
    "    (effects (font (size 1.27 1.27)) (justify %s))\n"
    "    (uuid %s)\n  )"
)

SHEET_PIN = (
    '    (pin "%s" %s (at %s %s 180)\n'
    "      (effects (font (size 1.27 1.27)) (justify right))\n"
    "      (uuid %s)\n    )"
)


def crossing_nets(sh):
    """Nets this sheet shares with another one, so they are its interface.

    Rails are left out: a power symbol is global by definition and does not
    belong in a sheet's signal interface. Everything else that leaves the
    sheet becomes a hierarchical label here and a pin on the sheet symbol,
    which is what makes six pages an actual hierarchy rather than six
    drawings that happen to share net names.
    """
    mine = {v for p in sh["parts"] for v in p["pins"].values()}
    others = set()
    for o in SHEETS:
        if o is sh:
            continue
        for p in o["parts"]:
            others.update(p["pins"].values())
    return sorted(n for n in mine & others if n not in RAILS)


LOCAL_LABEL = (
    '  (label "%s" (at %s %s %d)\n'
    "    (effects (font (size 1.27 1.27)) (justify left bottom))\n"
    "    (uuid %s)\n  )"
)


PWR_COUNTER = [0]


def emit_sheet(libs, sh, sheet_uuid, page):
    used = []
    for p in sh["parts"]:
        if p["lib_id"] not in used:
            used.append(p["lib_id"])
    for p in sh["parts"]:
        for net in p["pins"].values():
            lid = RAILS.get(net, (None,))[0]
            if lid and lid not in used:
                used.append(lid)
    lib_block = [libs.raw(lib_id) for lib_id in used]

    out = [
        "(kicad_sch (version %s) (generator eeschema)" % SCH_FORMAT_VERSION,
        "",
        "  (uuid %s)" % sheet_uuid,
        "",
        '  (paper "%s")' % sh.get("paper", "A3"),
        "",
        "  (title_block",
        '    (title "%s")' % TITLE,
        '    (date "%s")' % DATE,
        '    (rev "%s")' % REV,
        '    (company "%s")' % COMPANY,
        '    (comment 1 "%s -- %s")' % (sh["name"], sh["desc"]),
        "  )",
        "",
        "  (lib_symbols",
        "\n".join(lib_block),
        "  )",
        "",
    ]

    wires, labels, syms, ncs = [], [], [], []
    crossing = set(crossing_nets(sh))
    pwr_n = [PWR_COUNTER[0]]

    # Hand-drawn blocks: a pin the block's own wires reach is already
    # connected, so it drops its label. Deciding that per pin rather than per
    # net is what lets a block share a net with the rest of the sheet -- an
    # analog channel ends on AIN2, and the ADC over in the next column still
    # needs that name on its own pin.
    # Two passes: every block has to know which pins every other block has
    # wired before any of them can decide whether a name is private.
    blk_joined = set()
    for entry in sh.get("_blocks", []):
        blk = entry["blk"]
        for part, dx, dy in [(entry["anchor"], 0.0, 0.0)] + entry["members"]:
            for num, _nm, lx, ly, ang, hid in libs.pins(part["lib_id"]):
                if hid:
                    continue
                off, _d = pin_geometry(lx, ly, ang, part["theta"])
                px, py = dx + off[0], dy + off[1]
                if any(on_segment(px, py, a, b)
                       for poly in blk["wires"]
                       for a, b in zip(poly, poly[1:])):
                    blk_joined.add((part["ref"], num))
    for entry in sh.get("_blocks", []):
        blk, anchor = entry["blk"], entry["anchor"]
        ax, ay = anchor["x"], anchor["y"]
        # A wire must END at every junction on it. KiCad's own editor splits
        # wires when a junction is dropped, and its netlister relies on that:
        # a junction sitting mid-segment left the far half of the segment on
        # a net of its own -- SW stopped at the bootstrap cap and never
        # reached the inductor. Split here so the block tables stay readable.
        for i, poly in enumerate(blk["wires"]):
            for j, ((x1, y1), (x2, y2)) in enumerate(zip(poly, poly[1:])):
                cuts = [(jx, jy) for jx, jy in blk.get("junctions", [])
                        if min(x1, x2) <= jx <= max(x1, x2)
                        and min(y1, y2) <= jy <= max(y1, y2)
                        and (jx, jy) not in ((x1, y1), (x2, y2))]
                cuts.sort(key=lambda q: (q[0] - x1) ** 2 + (q[1] - y1) ** 2)
                pts = [(x1, y1)] + cuts + [(x2, y2)]
                for k, ((sx, sy), (ex, ey)) in enumerate(zip(pts, pts[1:])):
                    wires.append(wire_seg(ax + sx, ay + sy, ax + ex, ay + ey,
                                          det_uuid("bw:%s:%s:%d:%d:%d"
                                                   % (sh["file"], anchor["ref"],
                                                      i, j, k))))
        for k, (jx, jy) in enumerate(blk.get("junctions", [])):
            wires.append(junction(ax + jx, ay + jy,
                                  det_uuid("bj:%s:%s:%d"
                                           % (sh["file"], anchor["ref"], k))))
        # A name the block invents for its own wiring is a local label. A name
        # the rest of the design also uses has to be written the way the rest
        # of the design writes it, or ERC quite rightly complains that a local
        # and a global label share a name and mean different things.
        for net, spec in blk.get("labels", {}).items():
            lx, ly, ang = spec if len(spec) == 3 else spec + (0,)
            # Owning the net means the block's wires reach every pin on it --
            # not merely that every part is a member. The microSD connector
            # belongs to the SD block, but its VDD pin is fanned out to a
            # label like its eight neighbours, so SD_VDD is still a name the
            # sheet shares and has to be written as a global.
            elsewhere = {(p["ref"], num) for s2 in SHEETS for p in s2["parts"]
                         for num, v in p["pins"].items()
                         if v == net} - blk_joined
            uid = det_uuid("bl:%s:%s" % (sh["file"], net))
            if not elsewhere:
                labels.append(LOCAL_LABEL
                              % (net, mm(ax + lx), mm(ay + ly), ang, uid))
            elif net in crossing:
                labels.append(HIER_LABEL % (net, "bidirectional", mm(ax + lx),
                                            mm(ay + ly), ang, "left", uid))
            else:
                labels.append(
                    '  (global_label "%s" (shape input) (at %s %s %d) (fields_autoplaced)\n'
                    "    (effects (font (size 1.27 1.27)) (justify left))\n"
                    "    (uuid %s)\n"
                    '    (property "Intersheet References" "${INTERSHEET_REFS}" (at %s %s 0)\n'
                    "      (effects (font (size 1.27 1.27)) (justify left) hide)\n"
                    "    )\n  )"
                    % (net, mm(ax + lx), mm(ay + ly), ang, uid,
                       mm(ax + lx), mm(ay + ly)))
        # A rail pin the block wired up has lost its own power symbol, so the
        # block says where the rail enters instead: the inductor and the
        # feedback divider share one +5 V symbol on the output node, which is
        # what the node is.
        for net, lx, ly, facing in blk.get("rails", []):
            lib_id, shown = RAILS[net]
            sx, sy, stheta = power_placement(libs, lib_id, ax + lx, ay + ly,
                                             facing)
            pwr_n[0] += 1
            syms.append(emit_symbol(libs, sh, {
                "lib_id": lib_id, "value": shown, "voltage": "",
                "tolerance": "", "footprint": "", "mpn": "", "note": "",
                "prefix": "#PWR", "ref": "#PWR%03d" % pwr_n[0],
                "x": sx, "y": sy, "theta": stheta,
                "ext": symbol_extent(libs, lib_id, stheta),
                "_pwr_dir": facing,
            }, sheet_uuid))

    # Satellite links become a drawn wire, and both ends lose their label:
    # the connection is on the page now, so naming it twice adds nothing.
    sats = sh.get("_sats", {})
    joined, by_ref = set(blk_joined), {q["ref"]: q for q in sh["parts"]}
    for ref, info in sats.items():
        host, sat = by_ref[info["host"]], by_ref[ref]
        hoff, _hd, soff = info["wire"]
        hx, hy = host["x"] + hoff[0], host["y"] + hoff[1]
        sx, sy = sat["x"] + soff[0], sat["y"] + soff[1]
        wires.append(
            "  (wire (pts (xy %s %s) (xy %s %s))\n"
            "    (stroke (width 0) (type default))\n"
            "    (uuid %s)\n  )"
            % (mm(hx), mm(hy), mm(sx), mm(sy),
               det_uuid("link:%s:%s:%s" % (sh["file"], info["host"], ref))))
        # Both pin labels go and the name moves onto the wire, which is where
        # a schematic puts it. Dropping both without naming the wire would let
        # KiCad autoname the net Net-(U2-BST) and lose the meaning.
        labels.append(
            # The anchor has to sit exactly on the wire or KiCad treats the
            # label as floating; "left bottom" lifts the text clear instead.
            LOCAL_LABEL % (info["net"], mm(hx + (sx - hx) * 0.18),
                           mm(hy + (sy - hy) * 0.18), 0,
                           det_uuid("wlbl:%s:%s" % (sh["file"], ref))))
        joined.add((info["host"], info["host_pin"]))
        joined.add((ref, info["sat_pin"]))
    for p in sh["parts"]:
        syms.append(emit_symbol(libs, sh, p, sheet_uuid))
        for num, _, lx, ly, ang, hidden in libs.pins(p["lib_id"]):
            if hidden:
                continue  # KiCad bonds hidden power pins by name
            off, d = pin_geometry(lx, ly, ang, p["theta"])
            px, py = p["x"] + off[0], p["y"] + off[1]
            if num in p["nc"]:
                ncs.append("  (no_connect (at %s %s) (uuid %s))"
                           % (mm(px), mm(py), det_uuid("nc:%s:%s:%s" % (sh["file"], p["ref"], num))))
                continue
            net = p["pins"].get(num)
            if net is None:
                continue
            if (p["ref"], num) in joined:
                continue                   # already drawn as a wire
            ex, ey = px + d[0] * STUB, py + d[1] * STUB
            wires.append(
                "  (wire (pts (xy %s %s) (xy %s %s))\n"
                "    (stroke (width 0) (type default))\n"
                "    (uuid %s)\n  )"
                % (mm(px), mm(py), mm(ex), mm(ey),
                   det_uuid("wire:%s:%s:%s" % (sh["file"], p["ref"], num)))
            )
            # PWR_FLAG keeps a label. Giving it a power symbol instead pairs
            # the two into an island of their own that declares a rail and
            # connects to nothing you can see; a named label reads better and
            # joins the rail the same way.
            rail = None if p["prefix"].startswith("#") else RAILS.get(net)
            if rail:
                lib_id, shown = rail
                sx, sy, stheta = power_placement(libs, lib_id, ex, ey, d)
                pwr_n[0] += 1
                syms.append(emit_symbol(libs, sh, {
                    "lib_id": lib_id, "value": shown, "voltage": "",
                    "tolerance": "", "footprint": "", "mpn": "", "note": "",
                    "prefix": "#PWR", "ref": "#PWR%03d" % pwr_n[0],
                    "x": sx, "y": sy, "theta": stheta,
                    "ext": symbol_extent(libs, lib_id, stheta),
                    "_pwr_dir": d,
                }, sheet_uuid))
                continue
            if net in crossing:
                labels.append(
                    HIER_LABEL % (net, "bidirectional", mm(ex), mm(ey),
                                  label_rotation(d), label_justify(d),
                                  det_uuid("hlbl:%s:%s:%s"
                                           % (sh["file"], p["ref"], num))))
                continue
            labels.append(
                '  (global_label "%s" (shape input) (at %s %s %d) (fields_autoplaced)\n'
                "    (effects (font (size 1.27 1.27)) (justify %s))\n"
                "    (uuid %s)\n"
                '    (property "Intersheet References" "${INTERSHEET_REFS}" (at %s %s 0)\n'
                "      (effects (font (size 1.27 1.27)) (justify left) hide)\n"
                "    )\n  )"
                % (net, mm(ex), mm(ey), label_rotation(d), label_justify(d),
                   det_uuid("lbl:%s:%s:%s" % (sh["file"], p["ref"], num)), mm(ex), mm(ey))
            )

    PWR_COUNTER[0] = pwr_n[0]
    out += ncs + wires + labels + syms
    out.append("")
    out.append('  (sheet_instances\n    (path "/" (page "%d"))\n  )' % page)
    out.append(")")
    return "\n".join(out) + "\n"


def emit_root(sheet_uuids):
    out = [
        "(kicad_sch (version %s) (generator eeschema)" % SCH_FORMAT_VERSION,
        "",
        "  (uuid %s)" % ROOT_UUID,
        "",
        '  (paper "A3")',
        "",
        "  (title_block",
        '    (title "%s")' % TITLE,
        '    (date "%s")' % DATE,
        '    (rev "%s")' % REV,
        '    (company "%s")' % COMPANY,
        '    (comment 1 "Root sheet -- see the block sheets below")',
        "  )",
        "",
        "  (lib_symbols\n  )",
        "",
    ]
    y = 20.32
    root_wires, root_labels = [], []
    for i, sh in enumerate(SHEETS):
        su = sheet_uuids[sh["file"]]
        iface = crossing_nets(sh)
        height = max(25.0, 2.54 * (len(iface) + 2))
        pins = []
        for k, net in enumerate(iface):
            py = snap(y + 2.54 * (k + 1))
            pins.append(SHEET_PIN % (net, "bidirectional", mm(40.64), mm(py),
                                     det_uuid("spin:%s:%s" % (sh["file"], net))))
            # A named stub off each pin, so the top level joins the sheets by
            # name while every sheet still declares what it needs.
            root_wires.append(
                "  (wire (pts (xy %s %s) (xy %s %s))\n"
                "    (stroke (width 0) (type default))\n"
                "    (uuid %s)\n  )"
                % (mm(40.64), mm(py), mm(31.75), mm(py),
                   det_uuid("swire:%s:%s" % (sh["file"], net))))
            root_labels.append(
                '  (global_label "%s" (shape bidirectional) (at %s %s 180)'
                " (fields_autoplaced)\n"
                "    (effects (font (size 1.27 1.27)) (justify right))\n"
                "    (uuid %s)\n  )"
                % (net, mm(31.75), mm(py),
                   det_uuid("slbl:%s:%s" % (sh["file"], net))))
        block = (
            "  (sheet (at 40.64 %s) (size 120.65 %s) (fields_autoplaced)\n"
            "    (stroke (width 0.1524) (type solid))\n"
            "    (fill (color 0 0 0 0.0000))\n"
            "    (uuid %s)\n"
            '    (property "Sheetname" "%s" (at 40.64 %s 0)\n'
            "      (effects (font (size 1.27 1.27)) (justify left bottom))\n    )\n"
            '    (property "Sheetfile" "%s" (at 40.64 %s 0)\n'
            "      (effects (font (size 1.27 1.27)) (justify left top))\n    )\n"
            "    (instances\n"
            '      (project "%s"\n'
            '        (path "/%s" (page "%d"))\n'
            "      )\n    )"
            % (mm(y), mm(height), su, sh["name"], mm(y - 0.6), sh["file"],
               mm(y + height + 0.6), PROJECT, ROOT_UUID, i + 2)
        )
        if pins:
            block += "\n" + "\n".join(pins)
        out.append(block + "\n  )")
        y += height + 12.0
    out += root_wires + root_labels
    out.append("")
    out.append('  (sheet_instances\n    (path "/" (page "1"))\n  )')
    out.append(")")
    return "\n".join(out) + "\n"


PRO_TEMPLATE = """{
  "board": {"design_settings": {"rules": {"min_through_hole_diameter": 0.2}}},
  "boards": [],
  "cvpcb": {"equivalence_files": []},
  "libraries": {"pinned_footprint_libs": [], "pinned_symbol_libs": []},
  "meta": {"filename": "%s.kicad_pro", "version": 1},
  "net_settings": {
    "classes": [
      {"bus_width": 12, "clearance": 0.2, "diff_pair_gap": 0.25, "diff_pair_via_gap": 0.25,
       "diff_pair_width": 0.2, "line_style": 0, "microvia_diameter": 0.3, "microvia_drill": 0.1,
       "name": "Default", "pcb_color": "rgba(0, 0, 0, 0.000)", "schematic_color": "rgba(0, 0, 0, 0.000)",
       "track_width": 0.25, "via_diameter": 0.6, "via_drill": 0.3, "wire_width": 6},
      {"bus_width": 12, "clearance": 0.2, "diff_pair_gap": 0.25, "diff_pair_via_gap": 0.25,
       "diff_pair_width": 0.2, "line_style": 0, "microvia_diameter": 0.3, "microvia_drill": 0.1,
       "name": "Power", "pcb_color": "rgba(0, 0, 0, 0.000)", "schematic_color": "rgba(0, 0, 0, 0.000)",
       "track_width": 0.55, "via_diameter": 0.8, "via_drill": 0.4, "wire_width": 6},
      {"bus_width": 12, "clearance": 0.2, "diff_pair_gap": 0.2, "diff_pair_via_gap": 0.25,
       "diff_pair_width": 0.25, "line_style": 0, "microvia_diameter": 0.3, "microvia_drill": 0.1,
       "name": "CAN", "pcb_color": "rgba(0, 0, 0, 0.000)", "schematic_color": "rgba(0, 0, 0, 0.000)",
       "track_width": 0.25, "via_diameter": 0.6, "via_drill": 0.3, "wire_width": 6},
      {"bus_width": 12, "clearance": 0.2, "diff_pair_gap": 0.25, "diff_pair_via_gap": 0.25,
       "diff_pair_width": 0.2, "line_style": 0, "microvia_diameter": 0.3, "microvia_drill": 0.1,
       "name": "Fine", "pcb_color": "rgba(0, 0, 0, 0.000)", "schematic_color": "rgba(0, 0, 0, 0.000)",
       "track_width": 0.2, "via_diameter": 0.5, "via_drill": 0.25, "wire_width": 6}
    ],
    "meta": {"version": 3},
    "net_colors": null,
    "netclass_assignments": null,
    "netclass_patterns": [
      {"netclass": "Power", "pattern": "+VBAT"},
      {"netclass": "Power", "pattern": "+5V"},
      {"netclass": "Power", "pattern": "+3V3"},
      {"netclass": "Power", "pattern": "GND"},
      {"netclass": "Power", "pattern": "VBAT_IN"},
      {"netclass": "Power", "pattern": "VBAT_F"},
      {"netclass": "Power", "pattern": "VBAT_FB"},
      {"netclass": "Power", "pattern": "+5VS"},
      {"netclass": "Power", "pattern": "VBUS*"},
      {"netclass": "Power", "pattern": "SW_*"},
      {"netclass": "Power", "pattern": "SD_VDD"},
      {"netclass": "Power", "pattern": "LED_5V"},
      {"netclass": "Power", "pattern": "VSENS_F"},
      {"netclass": "Power", "pattern": "VSENS_SW"},
      {"netclass": "Fine", "pattern": "USB_CC1"},
      {"netclass": "Fine", "pattern": "USB_CC2"},
      {"netclass": "CAN", "pattern": "CAN_H"},
      {"netclass": "CAN", "pattern": "CAN_L"},
      {"netclass": "CAN", "pattern": "CANH_T"},
      {"netclass": "CAN", "pattern": "CANL_T"}
    ]
  },
  "pcbnew": {"last_paths": {}, "page_layout_descr_file": ""},
  "schematic": {
    "annotate_start_num": 0,
    "legacy_lib_dir": "",
    "legacy_lib_list": [],
    "meta": {"version": 1},
    "page_layout_descr_file": "",
    "spice_current_sheet_as_root": false,
    "spice_external_command": "spice \\"%%I\\"",
    "spice_model_current_sheet_as_root": true,
    "spice_save_all_currents": false,
    "spice_save_all_voltages": false,
    "subpart_first_id": 65,
    "subpart_id_separator": 0
  },
  "sheets": [],
  "text_variables": {}
}
"""


def write_bom(path):
    rows = []
    for sh in SHEETS:
        for p in sh["parts"]:
            if p["prefix"].startswith("#") or p["lib_id"] == "Connector:TestPoint":
                continue
            rows.append(p)
    groups = {}
    for p in rows:
        key = (p["value"], p.get("voltage", ""), p.get("tolerance", ""),
               p["footprint"], p["mpn"], p["lcsc"])
        groups.setdefault(key, []).append(p["ref"])
    with open(path, "w", newline="", encoding="utf-8") as fh:
        w = csv.writer(fh)
        w.writerow(["Qty (1 board)", "Qty (10 boards)", "References", "Value",
                    "Voltage", "Tolerance", "Footprint",
                    "Manufacturer part number", "LCSC", "Notes"])
        for (value, volt, tol, fp, mpn, lcsc), refs in sorted(
                groups.items(), key=lambda kv: kv[1][0]):
            note = next((p["note"] for p in rows if p["ref"] == refs[0] and p["note"]), "")
            w.writerow([len(refs), len(refs) * 10, " ".join(sorted(refs)),
                        value, volt, tol, fp, mpn, lcsc, note])
    return len(rows), len(groups)


def write_netlist(path, libs):
    nets = {}
    for sh in SHEETS:
        for p in sh["parts"]:
            for num, net in p["pins"].items():
                nets.setdefault(net, []).append("%s.%s" % (p["ref"], num))
    with open(path, "w", encoding="utf-8") as fh:
        fh.write("Net connectivity for %s rev %s\n" % (TITLE, REV))
        fh.write("(%d nets)\n\n" % len(nets))
        for net in sorted(nets):
            fh.write("%-14s %s\n" % (net, " ".join(sorted(nets[net]))))
    return nets


ROOT_UUID = det_uuid("root:" + PROJECT)


def main():
    ap = argparse.ArgumentParser()
    ap.add_argument("--symbol-dir", default=None,
                    help="KiCad symbol library directory "
                         "(auto-detected if omitted)")
    ap.add_argument("--out", default=os.path.join(os.path.dirname(__file__), ".."))
    args = ap.parse_args()

    if args.symbol_dir is None:
        args.symbol_dir = find_symbol_dir()
        if args.symbol_dir is None:
            raise SystemExit(
                "Could not find the KiCad symbol libraries.\n"
                "Pass --symbol-dir explicitly, e.g.\n"
                '  Windows: --symbol-dir "C:\\Program Files\\KiCad\\9.0'
                '\\share\\kicad\\symbols"\n'
                "  macOS:   --symbol-dir /Applications/KiCad/KiCad.app"
                "/Contents/SharedSupport/symbols\n"
                "  Linux:   --symbol-dir /usr/share/kicad/symbols")
        print("symbol libs : %s" % args.symbol_dir)

    libs = SymbolLibs(args.symbol_dir)
    libs.symbol("Device:R")  # force one library load so the format is known
    if libs.lib_version != VALIDATED_SYMBOL_VERSION:
        print(
            "WARNING: symbol libraries in %s are format %s, but the embedded\n"
            "         definitions were last validated against %s (KiCad 9.0).\n"
            "         A different library generation may use syntax the emitted\n"
            "         schematic format (%s) does not accept. Run gen/validate.py\n"
            "         before trusting the output."
            % (args.symbol_dir, libs.lib_version, VALIDATED_SYMBOL_VERSION,
               SCH_FORMAT_VERSION))

    # The KiCad 9 libraries moved the generic MOSFET symbols out of Device.
    # Resolve each part against whichever library the local install has; the
    # symbols are pin-identical, so this only changes the recorded lib_id.
    alternates = {
        "Device:Q_NMOS_GSD": ("Transistor_FET:Q_NMOS_GSD",),
        "Device:Q_PMOS_GSD": ("Transistor_FET:Q_PMOS_GSD",),
        "Device:Q_PNP_BEC": ("Transistor_BJT:Q_PNP_BEC",),
    }
    resolved = {}
    for sh in SHEETS:
        for p in sh["parts"]:
            lid = p["lib_id"]
            if lid not in resolved:
                resolved[lid] = lid
                if not libs.has(lid):
                    for alt in alternates.get(lid, ()):
                        if libs.has(alt):
                            print("symbol %s not in these libraries; using %s"
                                  % (lid, alt))
                            resolved[lid] = alt
                            break
            p["lib_id"] = resolved[lid]

    assign_refs()
    place(libs)

    out = os.path.abspath(args.out)
    os.makedirs(out, exist_ok=True)

    sheet_uuids = {sh["file"]: det_uuid("sheet:" + sh["file"]) for sh in SHEETS}
    open(os.path.join(out, PROJECT + ".kicad_sch"), "w", encoding="utf-8").write(
        emit_root(sheet_uuids))
    for i, sh in enumerate(SHEETS):
        open(os.path.join(out, sh["file"]), "w", encoding="utf-8").write(
            emit_sheet(libs, sh, sheet_uuids[sh["file"]], i + 2))
    open(os.path.join(out, PROJECT + ".kicad_pro"), "w", encoding="utf-8").write(
        PRO_TEMPLATE % PROJECT)

    n_parts, n_lines = write_bom(os.path.join(out, "bom.csv"))
    nets = write_netlist(os.path.join(out, "netlist.txt"), libs)

    print("sheets      : %d" % (len(SHEETS) + 1))
    print("components  : %d (%d distinct BOM lines)" % (n_parts, n_lines))
    print("nets        : %d" % len(nets))
    singles = [n for n, v in nets.items() if len(v) < 2]
    if singles:
        print("single-node nets (check these): %s" % ", ".join(sorted(singles)))


if __name__ == "__main__":
    main()
